masaccio/picow_day_clock/kicad/pico_dow_clock/pico_dow_clock.kicad_sch

## KiCad design kicad/pico_dow_clock/pico_dow_clock.kicad_sch (2026-08-09)

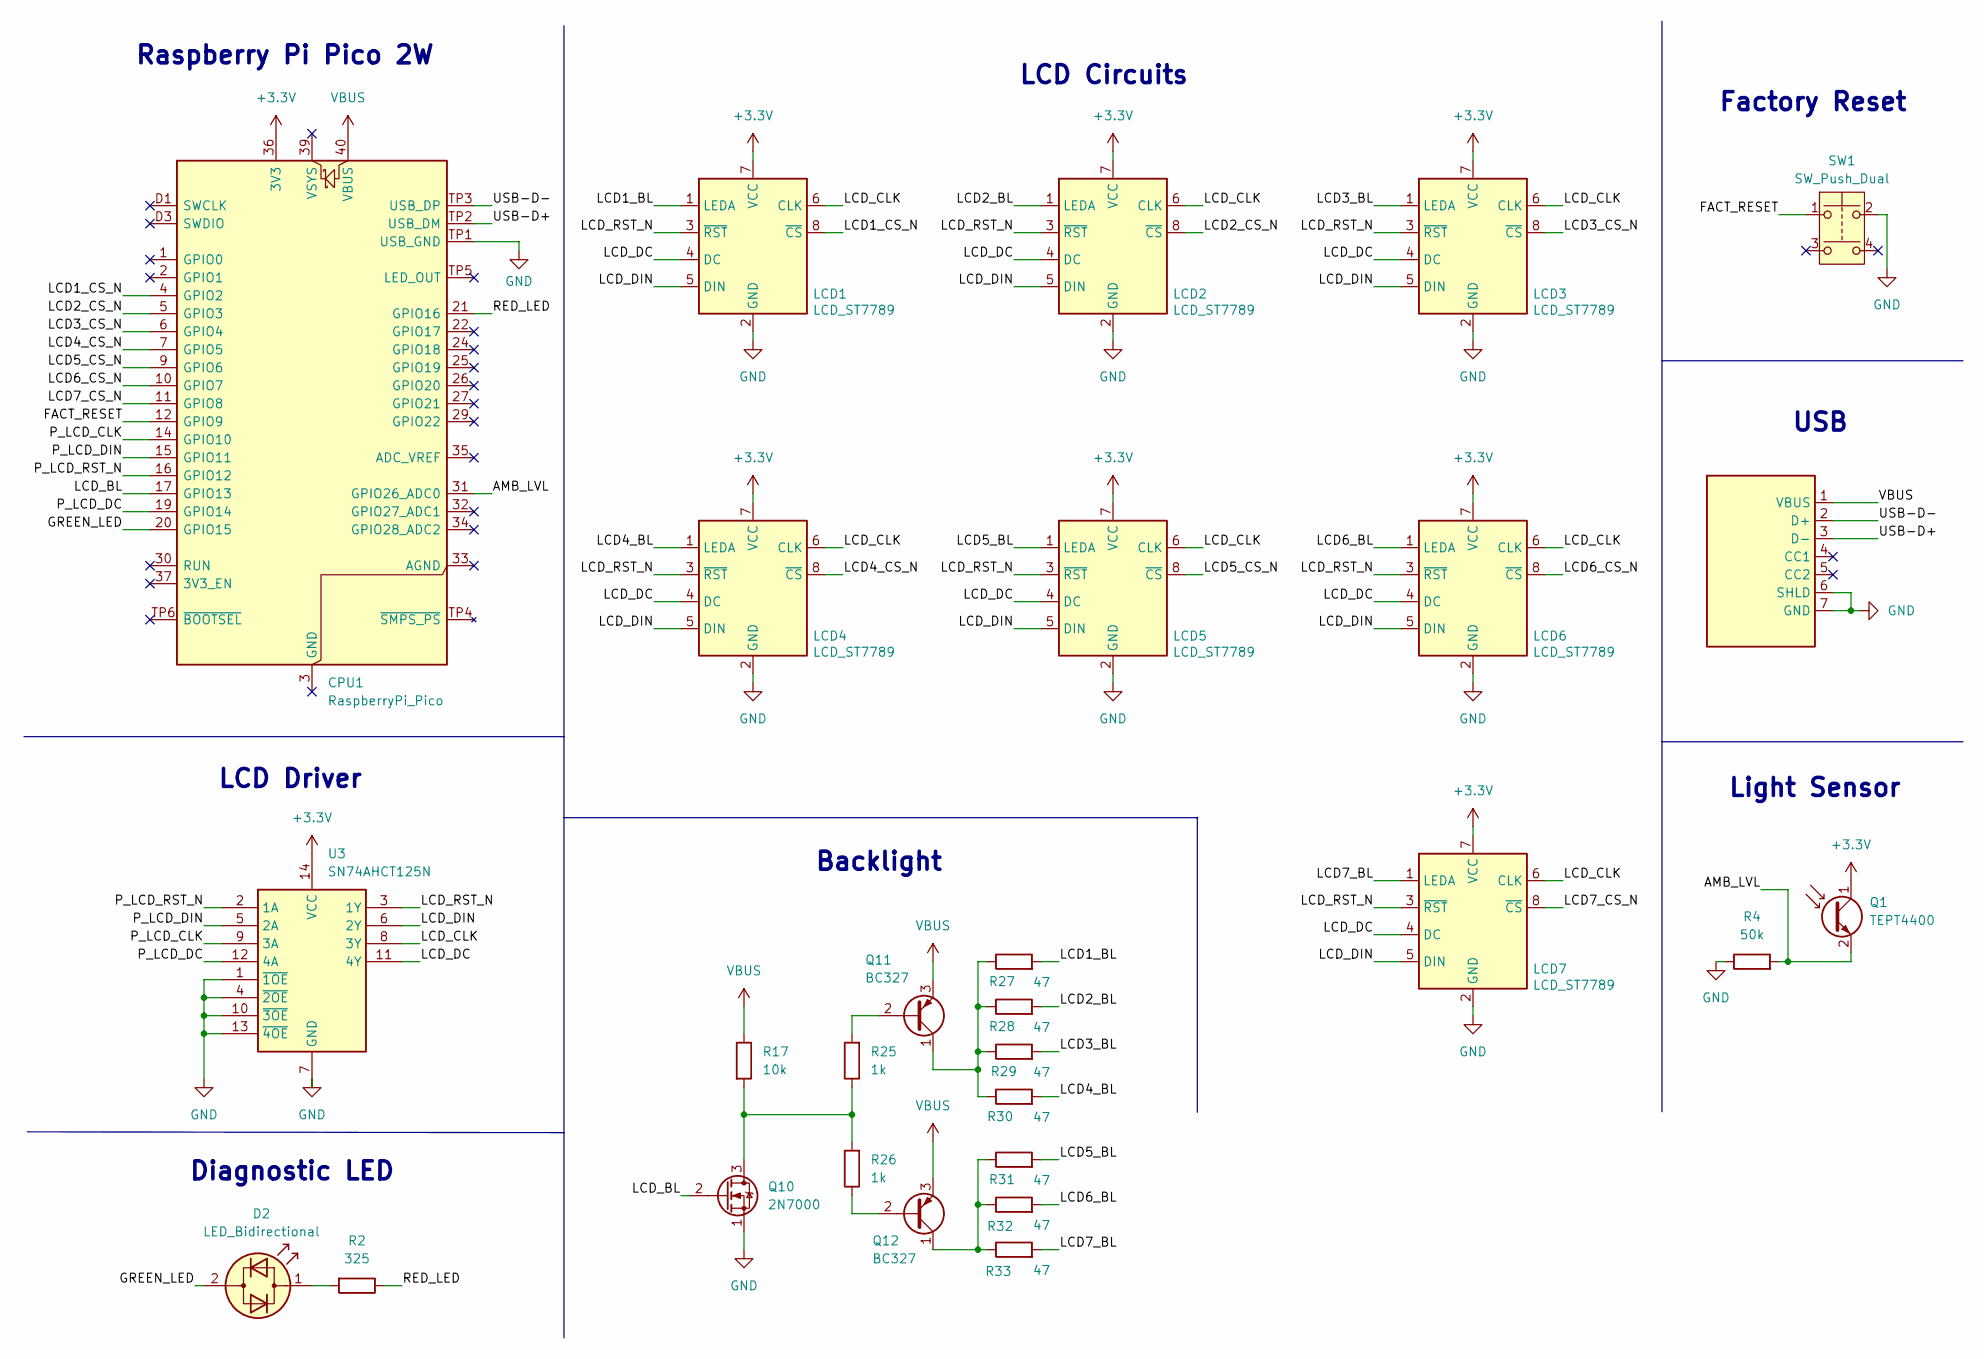
[picture p7: schematic pico_dow_clock.kicad_sch]

Parts:
CPU1: RaspberryPi_Pico; RaspberryPi_Pico_Original_SMD
D2: LED_Bidirectional
LCD1, LCD2, LCD3, LCD4, LCD5, LCD6, LCD7: LCD_ST7789
Q1: TEPT4400; LED_D3.0mm_Clear
Q10: 2N7000; TO-92_Inline
Q11, Q12: BC327; TO-92_Inline
R2: 325; R_Axial_DIN0207_L6.3mm_D2.5mm_P7.62mm_Horizontal
R4: 50k; R_Axial_DIN0207_L6.3mm_D2.5mm_P7.62mm_Horizontal
R17: 10k; R_Axial_DIN0207_L6.3mm_D2.5mm_P7.62mm_Horizontal
R25, R26: 1k; R_Axial_DIN0207_L6.3mm_D2.5mm_P7.62mm_Horizontal
R27, R28, R29, R30, R31, R32, R33: 47; R_Axial_DIN0207_L6.3mm_D2.5mm_P7.62mm_Horizontal
SW1: SW_Push_Dual
U3: SN74AHCT125N
USB1: Sparkfun_BOB_23055

Connections:
+3.3V: CPU1.36 (3V3), LCD1.7 (VCC), LCD2.7 (VCC), LCD3.7 (VCC), LCD4.7 (VCC), LCD5.7 (VCC), LCD6.7 (VCC), LCD7.7 (VCC), Q1.1 (C), U3.14 (VCC)
AMB_LVL: CPU1.31 (GPIO26_ADC0), Q1.2 (E), R4.2
FACT_RESET: CPU1.12 (GPIO9), SW1.1
GND: CPU1.TP1 (USB_GND), LCD1.2 (GND), LCD2.2 (GND), LCD3.2 (GND), LCD4.2 (GND), LCD5.2 (GND), LCD6.2 (GND), LCD7.2 (GND), Q10.1 (S), R4.1, SW1.2, U3.1 (~1OE), U3.4 (~2OE), U3.7 (GND), U3.10 (~3OE), U3.13 (~4OE), USB1.6 (SHLD), USB1.7 (GND)
GREEN_LED: CPU1.20 (GPIO15), D2.2 (AK)
LCD1_BL: LCD1.1 (LEDA), R27.2
LCD1_CS_N: CPU1.4 (GPIO2), LCD1.8 (~CS)
LCD2_BL: LCD2.1 (LEDA), R28.2
LCD2_CS_N: CPU1.5 (GPIO3), LCD2.8 (~CS)
LCD3_BL: LCD3.1 (LEDA), R29.2
LCD3_CS_N: CPU1.6 (GPIO4), LCD3.8 (~CS)
LCD4_BL: LCD4.1 (LEDA), R30.2
LCD4_CS_N: CPU1.7 (GPIO5), LCD4.8 (~CS)
LCD5_BL: LCD5.1 (LEDA), R31.2
LCD5_CS_N: CPU1.9 (GPIO6), LCD5.8 (~CS)
LCD6_BL: LCD6.1 (LEDA), R32.2
LCD6_CS_N: CPU1.10 (GPIO7), LCD6.8 (~CS)
LCD7_BL: LCD7.1 (LEDA), R33.2
LCD7_CS_N: CPU1.11 (GPIO8), LCD7.8 (~CS)
LCD_BL: CPU1.17 (GPIO13), Q10.2 (G)
LCD_CLK: LCD1.6 (CLK), LCD2.6 (CLK), LCD3.6 (CLK), LCD4.6 (CLK), LCD5.6 (CLK), LCD6.6 (CLK), LCD7.6 (CLK), U3.8 (3Y)
LCD_DC: LCD1.4 (DC), LCD2.4 (DC), LCD3.4 (DC), LCD4.4 (DC), LCD5.4 (DC), LCD6.4 (DC), LCD7.4 (DC), U3.11 (4Y)
LCD_DIN: LCD1.5 (DIN), LCD2.5 (DIN), LCD3.5 (DIN), LCD4.5 (DIN), LCD5.5 (DIN), LCD6.5 (DIN), LCD7.5 (DIN), U3.6 (2Y)
LCD_RST_N: LCD1.3 (~RST), LCD2.3 (~RST), LCD3.3 (~RST), LCD4.3 (~RST), LCD5.3 (~RST), LCD6.3 (~RST), LCD7.3 (~RST), U3.3 (1Y)
unnamed: CPU1.3 (GND), CPU1.8 (GND), CPU1.13 (GND), CPU1.18 (GND), CPU1.23 (GND), CPU1.28 (GND), CPU1.38 (GND), CPU1.D2 (GND)
unnamed: D2.1 (KA), R2.2
unnamed: Q10.3 (D), R17.2, R25.1, R26.2
unnamed: Q11.1 (C), R27.1, R28.1, R29.1, R30.1
unnamed: Q11.2 (B), R25.2
unnamed: Q12.1 (C), R31.1, R32.1, R33.1
unnamed: Q12.2 (B), R26.1
P_LCD_CLK: CPU1.14 (GPIO10), U3.9 (3A)
P_LCD_DC: CPU1.19 (GPIO14), U3.12 (4A)
P_LCD_DIN: CPU1.15 (GPIO11), U3.5 (2A)
P_LCD_RST_N: CPU1.16 (GPIO12), U3.2 (1A)
RED_LED: CPU1.21 (GPIO16), R2.1
USB-D+: CPU1.TP2 (USB_DM), USB1.3 (D-)
USB-D-: CPU1.TP3 (USB_DP), USB1.2 (D+)
VBUS: CPU1.40 (VBUS), Q11.3 (E), Q12.3 (E), R17.1, USB1.1 (VBUS)

Notes on the sheet:
Diagnostic LED
Factory Reset
USB
Raspberry Pi Pico 2W
LCD Circuits
LCD Driver
Light Sensor
Backlight
