masaccio/picow_day_clock/src/lcd.c

/*
 * SPDX-License-Identifier: MIT
 *
 * Much of this code is derived from the Waveshare 1.47inch LCD Module
 * driver (see https://www.waveshare.com/wiki/1.47inch_LCD_Module).
 *
 * (c) 2022 Waveshare team
 *
 * Additional code:
 *
 * (c) 2025 Jon Connell
 *
 */

#include <stdarg.h>
#include <stdio.h>
#include <stdlib.h>
#include <string.h>

// PICO SDK
#ifndef TEST_MODE
#include "hardware/pwm.h"
#include "hardware/spi.h"
#include "pico/stdlib.h"
#else
#include "mock.h"
#endif

// Local includes
#include "bitmap.h"
#include "clock.h"
#include "config.h"

// How the 2-bit colours map to 16-bit colour
static uint16_t color_table[] = LCD_COLOR_TABLE;

// PWM slice attached to the backlight
static uint slice_num;

// Current line number for diagnostics
static uint8_t line_number = 0;

// Shared line buffer to write a line at a time with spi_write_blocking()
uint8_t linebuf[LCD_WIDTH * 2];

static void st7789_init(lcd_state_t *state);

static void lcd_reset(lcd_state_t *state);

void lcd_write_image(lcd_state_t *state, const uint8_t *image, uint16_t x_start, uint16_t y_start, uint16_t image_width,
                     uint16_t image_height, color_t fg_color);

int lcd_write_char(lcd_state_t *state, uint16_t x_point, uint16_t y_point, const char ascii_char, font_t *font,
                   color_t fg_color, color_t bg_color);

lcd_state_t *lcd_init(lcd_state_t *state, uint16_t lcd_num, bool reset)

{
    state->RST_N_gpio = LCD_GPIO_RST_N;
    state->DC_gpio = LCD_GPIO_DC;
    state->BL_gpio = LCD_GPIO_BL;
    state->CS_N_gpio = LCD_GPIO_CS_N_BASE + lcd_num;
    state->CLK_gpio = LCD_GPIO_CLK;
    state->MOSI_gpio = LCD_GPIO_MOSI;
    state->smoothed_adc = 0;

    lcd_init_peripherals(state, reset);
    lcd_set_backlight(state, 90);
    if (reset) {
        // All displays share the same reset line
        lcd_reset(state);
    }

    st7789_init(state);
    lcd_clear_screen(state, BG_COLOR);

    return state;
}

void lcd_print_line(lcd_state_t *state, color_t color, lcd_status_message_t msg)
{
    uint16_t y_start = (line_number + 3) * text_font.height;
    uint16_t x_point = 0;
    uint16_t y_point = y_start;
    int width = 0;
    const char *msg_str;
    switch (msg) {
        case LCD_MSG_INIT_OK:
            msg_str = LCD_MSG_STR_INIT_OK;
            break;
        case LCD_MSG_FLASH_ERROR:
            msg_str = LCD_MSG_STR_FLASH_ERROR;
            break;
        case LCD_MSG_WIFI_ERROR:
            msg_str = LCD_MSG_STR_WIFI_ERROR;
            break;
        case LCD_MSG_WIFI_OK:
            msg_str = LCD_MSG_STR_WIFI_OK;
            break;
    }
    while (*msg_str != '\0') {
        // Wrap end of line
        if ((x_point + width) > LCD_WIDTH) {
            x_point = 0;
            y_point += text_font.height;
        }

        // Wrap end of screen
        if ((y_point + text_font.height) > LCD_HEIGHT) {
            x_point = 0;
            y_point = 0;
        }
        width = lcd_write_char(state, x_point, y_point, *msg_str, &text_font, color, BG_COLOR);
        x_point += width;
        msg_str++;
    }
    line_number++;
}

void lcd_print_clock_digit(lcd_state_t *state, color_t color, const char ascii_char)
{
    if (ascii_char < ' ' || ascii_char > '~') {
        return;
    }
    const font_glyph_t entry = clock_digit_font.table[ascii_char - ' '];
    uint16_t x_point = (LCD_WIDTH - entry.width) / 2;
    (void)lcd_write_char(state, x_point, 0, ascii_char, &clock_digit_font, color, BLACK);
}

#define ICON_CASE(STATUS, ICON, OFFSET, COLOR)                                                                         \
    case STATUS:                                                                                                       \
        lcd_write_image(state, ICON, OFFSET, 0, ICON_SIZE, ICON_SIZE, COLOR);                                          \
        break;

void lcd_update_icons(lcd_state_t *state, watchdog_error_t watchdog_error, ntp_error_t ntp_error,
                      wifi_error_t wifi_error)
{
    switch (watchdog_error) {
        ICON_CASE(WATCHDOG_RESET, watchdog_icon, WATCHDOG_ICON_X_OFFSET, RED)
        ICON_CASE(WATCHDOG_NTP, watchdog_ntp_icon, WATCHDOG_ICON_X_OFFSET, RED)
        ICON_CASE(WATCHDOG_WIFI, watchdog_wifi_icon, WATCHDOG_ICON_X_OFFSET, RED)
        case WATCHDOG_OK:
            break;
    }
    switch (ntp_error) {
        ICON_CASE(NTP_OK, ntp_icon, NTP_ICON_X_OFFSET, GREEN)
        ICON_CASE(NTP_INIT_ERROR, ntp_init_icon, NTP_ICON_X_OFFSET, RED)
        ICON_CASE(NTP_DNS_ERROR, ntp_dns_icon, NTP_ICON_X_OFFSET, RED)
        ICON_CASE(NTP_MEMORY_ERROR, ntp_memory_icon, NTP_ICON_X_OFFSET, RED)
        ICON_CASE(NTP_PROTOCOL_ERROR, ntp_error_icon, NTP_ICON_X_OFFSET, RED)
        ICON_CASE(NTP_TIMEOUT_ERROR, ntp_timeout_icon, NTP_ICON_X_OFFSET, RED)
    }
    switch (wifi_error) {
        ICON_CASE(WIFI_OK, wifi_icon, WIFI_ICON_X_OFFSET, GREEN)
        ICON_CASE(WIFI_INIT_ERROR, wifi_init_icon, WIFI_ICON_X_OFFSET, RED)
        ICON_CASE(WIFI_TIMEOUT_ERROR, wifi_timeout_icon, WIFI_ICON_X_OFFSET, RED)
        ICON_CASE(WIFI_AUTH_ERROR, wifi_password_icon, WIFI_ICON_X_OFFSET, RED)
        ICON_CASE(WIFI_CONNECT_ERROR, wifi_connect_icon, WIFI_ICON_X_OFFSET, RED)
        ICON_CASE(WIFI_UNKNOWN_ERROR, wifi_error_icon, WIFI_ICON_X_OFFSET, RED)
    }
}

// Initialise the Pico peripherals we will use (SPI, GPIO, PWM)
void lcd_init_peripherals(lcd_state_t *state, int reset)
{
    spi_init(spi1, 10000 * 1000);
    gpio_set_function(state->CLK_gpio, GPIO_FUNC_SPI);
    gpio_set_function(state->MOSI_gpio, GPIO_FUNC_SPI);

    if (reset) {
        gpio_init(state->RST_N_gpio);
        gpio_set_dir(state->RST_N_gpio, GPIO_OUT);
    }
    gpio_init(state->DC_gpio);
    gpio_set_dir(state->DC_gpio, GPIO_OUT);
    gpio_init(state->CS_N_gpio);
    gpio_set_dir(state->CS_N_gpio, GPIO_OUT);
    gpio_init(state->BL_gpio);
    gpio_set_dir(state->BL_gpio, GPIO_OUT);

    gpio_put(state->CS_N_gpio, 1);
    gpio_put(state->DC_gpio, 0);
    gpio_put(state->BL_gpio, 1);

    gpio_set_function(state->BL_gpio, GPIO_FUNC_PWM);
    slice_num = (uint)pwm_gpio_to_slice_num(state->BL_gpio);
    pwm_set_wrap(slice_num, 100);
    pwm_set_chan_level(slice_num, PWM_CHAN_B, 1);
    pwm_set_clkdiv(slice_num, 50);
    pwm_set_enabled(slice_num, 1);
}

// Use the PWM to set the backlight level for all displays
void lcd_set_backlight(lcd_state_t *state, uint8_t level)
{
    (void)state;
    if (level > 100) {
        level = 100;
    }
    pwm_set_chan_level(slice_num, PWM_CHAN_B, level);
}

// Cycle reset for all displays
static void lcd_reset(lcd_state_t *state)
{
    gpio_put(state->RST_N_gpio, 1);
    sleep_ms(100);
    gpio_put(state->RST_N_gpio, 0);
    sleep_ms(100);
    gpio_put(state->RST_N_gpio, 1);
    sleep_ms(100);
}

// Select an LCD and send a command byte
static void st7789_command(lcd_state_t *state, uint8_t reg)
{
    gpio_put(state->DC_gpio, 0);
    gpio_put(state->CS_N_gpio, 0);
    spi_write_blocking(spi1, &reg, 1);
    gpio_put(state->CS_N_gpio, 1);
}

// Select an LCD and send a data byte
static void st7789_data_byte(lcd_state_t *state, uint8_t data)
{
    gpio_put(state->DC_gpio, 1);
    gpio_put(state->CS_N_gpio, 0);
    spi_write_blocking(spi1, &data, 1);
    gpio_put(state->CS_N_gpio, 1);
}

static void st7789_init(lcd_state_t *state)
{

    st7789_command(state, 0x11); // SLPOUT (Sleep Out)

    sleep_ms(120);

    st7789_command(state, 0x36); // MADCTL (Memory Data Access Control)
    st7789_data_byte(state, 0x00);

    st7789_command(state, 0x3A); // COLMOD (Interface Pixel Format)
    st7789_data_byte(state, 0x05);

    st7789_command(state, 0xB2); // PORCTRL (Porch Setting)
    st7789_data_byte(state, 0x0C);
    st7789_data_byte(state, 0x0C);
    st7789_data_byte(state, 0x00);
    st7789_data_byte(state, 0x33);
    st7789_data_byte(state, 0x33);

    st7789_command(state, 0xB7); // GCTRL (Gate Control)
    st7789_data_byte(state, 0x35);

    st7789_command(state, 0xBB); // VCOMS (VCOM Setting)
    st7789_data_byte(state, 0x35);

    st7789_command(state, 0xC0); // LCMCTRL (LCM Control)
    st7789_data_byte(state, 0x2C);

    st7789_command(state, 0xC2); // VDVVRHEN (VDV and VRH Command Enable)
    st7789_data_byte(state, 0x01);

    st7789_command(state, 0xC3); // VRHS (VRH Set)
    st7789_data_byte(state, 0x13);

    st7789_command(state, 0xC4); // VDVS (VDV Set)
    st7789_data_byte(state, 0x20);

    st7789_command(state, 0xC6); // FRCTRL2 (Frame Rate Control in Normal Mode)
    st7789_data_byte(state, 0x0F);

    st7789_command(state, 0xD0); // PWCTRL1 (Power Control 1)
    st7789_data_byte(state, 0xA4);
    st7789_data_byte(state, 0xA1);

    st7789_command(state, 0xD6); // !!! Non-standard command
    st7789_data_byte(state, 0xA1);

    st7789_command(state, 0xE0); // PVGAMCTRL (Positive Voltage Gamma Control)
    st7789_data_byte(state, 0xF0);
    st7789_data_byte(state, 0x00);
    st7789_data_byte(state, 0x04);
    st7789_data_byte(state, 0x04);
    st7789_data_byte(state, 0x04);
    st7789_data_byte(state, 0x05);
    st7789_data_byte(state, 0x33);
    st7789_data_byte(state, 0x3E);
    st7789_data_byte(state, 0x38);
    st7789_data_byte(state, 0x12);
    st7789_data_byte(state, 0x12);
    st7789_data_byte(state, 0x28);
    st7789_data_byte(state, 0x30);

    st7789_command(state, 0xE1); // NVGAMCTRL (Negative Voltage Gamma Control)
    st7789_data_byte(state, 0xF0);
    st7789_data_byte(state, 0x07);
    st7789_data_byte(state, 0x0A);
    st7789_data_byte(state, 0x0D);
    st7789_data_byte(state, 0x0B);
    st7789_data_byte(state, 0x07);
    st7789_data_byte(state, 0x28);
    st7789_data_byte(state, 0x33);
    st7789_data_byte(state, 0x3E);
    st7789_data_byte(state, 0x36);
    st7789_data_byte(state, 0x14);
    st7789_data_byte(state, 0x14);
    st7789_data_byte(state, 0x32);

    st7789_command(state, 0x21); // INVON (Display Inversion On)

    st7789_command(state, 0x11); // SLPOUT (Sleep Out)

    sleep_ms(120);

    st7789_command(state, 0x29); // DISPON (Display On)
}

static void st7789_set_command_windows(lcd_state_t *state, uint16_t x_start, uint16_t y_start, uint16_t width,
                                       uint16_t height)
{

    // X-coordinates are based on portrait mode
    st7789_command(state, 0x2A); // CASET (Column address set)
    st7789_data_byte(state, (x_start + LCD_ROW_START) >> 8);
    st7789_data_byte(state, (x_start + LCD_ROW_START) & 0xff);
    st7789_data_byte(state, (x_start + width + LCD_ROW_START - 1) >> 8);
    st7789_data_byte(state, (x_start + width + LCD_ROW_START - 1) & 0xff);

    // Set the Y coordinates
    st7789_command(state, 0x2B); // RASET (Row address set)
    st7789_data_byte(state, (y_start + LCD_COL_START) >> 8);
    st7789_data_byte(state, (y_start + LCD_COL_START) & 0xff);
    st7789_data_byte(state, (y_start + height + LCD_COL_START - 1) >> 8);
    st7789_data_byte(state, (y_start + height + LCD_COL_START - 1) & 0xff);

    st7789_command(state, 0x2C); // RAMWR (Memory Write)
}

void lcd_draw_rectangle(lcd_state_t *state, uint16_t x_start, uint16_t y_start, uint16_t width, uint16_t height,
                        uint16_t fg_color)
{
    st7789_set_command_windows(state, x_start, y_start, width, height);
    gpio_put(state->DC_gpio, 1);
    gpio_put(state->CS_N_gpio, 0);

    uint8_t fg_hi = color_table[fg_color % 4] >> 8;
    uint8_t fg_lo = color_table[fg_color % 4] & 0xFF;
    for (uint16_t x = 0; x < width; x++) {
        linebuf[x * 2] = fg_hi;
        linebuf[x * 2 + 1] = fg_lo;
    }

    for (uint16_t j = 0; j < height; j++) {
        spi_write_blocking(spi1, (uint8_t *)linebuf, width * 2);
    }
    gpio_put(state->CS_N_gpio, 1);
}

void lcd_clear_screen(lcd_state_t *state, uint16_t color)
{
    line_number = 0;
    lcd_draw_rectangle(state, 0, 0, LCD_WIDTH, LCD_HEIGHT, color);
}

int lcd_write_char(lcd_state_t *state, uint16_t x_point, uint16_t y_point, const char ascii_char, font_t *font,
                   color_t fg_color, color_t bg_color)
{
    if (ascii_char < ' ' || ascii_char > '~') {
        return 0;
    }
    const font_glyph_t *entry = &font->table[ascii_char - ' '];
    const uint8_t *ptr = entry->table;
    uint16_t font_width = entry->width;

    st7789_set_command_windows(state, x_point, y_point, font_width, font->height);
    gpio_put(state->DC_gpio, 1);
    gpio_put(state->CS_N_gpio, 0);

    uint8_t fg_hi = color_table[fg_color % 4] >> 8;
    uint8_t fg_lo = color_table[fg_color % 4] & 0xFF;
    uint8_t bg_hi = color_table[bg_color % 4] >> 8;
    uint8_t bg_lo = color_table[bg_color % 4] & 0xFF;

    for (uint16_t glyph_row = 0; glyph_row < font->height; glyph_row++) {
        for (uint16_t glyph_column = 0; glyph_column < font_width; glyph_column++) {
            uint8_t glyph_pixels = *(ptr + (glyph_column / 8));
            if (glyph_pixels & (0x80 >> (glyph_column % 8))) {
                linebuf[glyph_column * 2] = fg_hi;
                linebuf[glyph_column * 2 + 1] = fg_lo;
            } else {
                linebuf[glyph_column * 2] = bg_hi;
                linebuf[glyph_column * 2 + 1] = bg_lo;
            }
        }
        spi_write_blocking(spi1, (uint8_t *)linebuf, font_width * 2);
        ptr += font->byte_width;
    }

    gpio_put(state->CS_N_gpio, 1);

    return font_width;
}

void lcd_write_image(lcd_state_t *state, const uint8_t *image, uint16_t x_start, uint16_t y_start, uint16_t image_width,
                     uint16_t image_height, color_t fg_color)
{
    st7789_set_command_windows(state, x_start, y_start, image_width, image_height);
    gpio_put(state->DC_gpio, 1);
    gpio_put(state->CS_N_gpio, 0);

    int bytes_per_row = (image_width + 7) / 8;
    for (int yy = 0; yy < image_height; yy++) {
        for (int byte_idx = 0; byte_idx < bytes_per_row; byte_idx++) {
            uint8_t byte = *image++;
            for (int bit = 0; bit < 8; bit++) {
                int x = x_start + (byte_idx * 8) + bit;
                if (x < x_start + image_width) {
                    // Most significant bit is left-most pixel
                    linebuf[(x - x_start) * 2] = color_table[(byte & (1 << (7 - bit))) ? fg_color : 0] >> 8;
                    linebuf[(x - x_start) * 2 + 1] = color_table[(byte & (1 << (7 - bit))) ? fg_color : 0] & 0xFF;
                }
            }
        }
        spi_write_blocking(spi1, (uint8_t *)linebuf, image_width * 2);
    }
    gpio_put(state->CS_N_gpio, 1);
}
