masaccio/picow_day_clock/src/bitmap.h

#pragma once

#include <stdint.h>

typedef struct
{
    const uint8_t *table;
    const uint8_t width;
} font_glyph_t;

typedef struct
{
    const font_glyph_t *table;
    uint16_t byte_width;
    uint16_t height;
} font_t;

extern font_t text_font;
extern font_t clock_digit_font;

#define ICON_SIZE 36
#define BYTES_PER_ROW (ICON_SIZE + 7) / 8
#define ICON_BYTES (BYTES_PER_ROW * ICON_SIZE)

// Allow 5 pixels for the rounded edge
#define WATCHDOG_ICON_X_OFFSET (uint16_t)(LCD_WIDTH - 5 + ICON_SIZE * -3)
#define NTP_ICON_X_OFFSET (uint16_t)(LCD_WIDTH - 5 + ICON_SIZE * -2)
#define WIFI_ICON_X_OFFSET (uint16_t)(LCD_WIDTH - 5 + ICON_SIZE * -1)

extern const uint8_t memory_icon[ICON_BYTES];
extern const uint8_t watchdog_icon[ICON_BYTES];
extern const uint8_t watchdog_wifi_icon[ICON_BYTES];
extern const uint8_t watchdog_ntp_icon[ICON_BYTES];
extern const uint8_t wifi_icon[ICON_BYTES];
extern const uint8_t ntp_icon[ICON_BYTES];
extern const uint8_t wifi_init_icon[ICON_BYTES];
extern const uint8_t wifi_timeout_icon[ICON_BYTES];
extern const uint8_t wifi_password_icon[ICON_BYTES];
extern const uint8_t wifi_connect_icon[ICON_BYTES];
extern const uint8_t wifi_error_icon[ICON_BYTES];
extern const uint8_t ntp_init_icon[ICON_BYTES];
extern const uint8_t ntp_dns_icon[ICON_BYTES];
extern const uint8_t ntp_timeout_icon[ICON_BYTES];
extern const uint8_t ntp_memory_icon[ICON_BYTES];
extern const uint8_t ntp_error_icon[ICON_BYTES];
