masaccio/picow_day_clock/tests/tests.c

#include <stdbool.h>
#include <stdio.h>
#include <stdlib.h>
#include <string.h>
#include <time.h>

#include "clock.h"
#include "config.h"
#include "test.h"

// These system calls have been redefined in mock.h so undef them here
// so that we can call into the system libraries as needed.
#undef printf
#undef calloc
#undef free

typedef int (*test_func_t)(void);
static unsigned int test_verbose = 0;

mock_context_t mock_ctx = {0};
#define RESET_MOCK_CONFIG()                                                                                            \
    do {                                                                                                               \
        memset((void *)&mock_ctx.inject, 0, sizeof(mock_ctx.inject));                                                  \
        memset((void *)&mock_ctx.spy, 0, sizeof(mock_ctx.spy));                                                        \
        mock_ctx.sim.dns_pending = false;                                                                              \
        mock_ctx.sim.udp_pending = false;                                                                              \
        mock_ctx.sim.clock_timer_active = false;                                                                       \
        mock_ctx.sim.backlight_timer_active = false;                                                                   \
        icon_queue_t_init(&mock_ctx.spy.icon_history);                                                                 \
        lcd_message_queue_t_init(&mock_ctx.spy.lcd_msg_history);                                                       \
    } while (0)

#define TEST_AP_SSID "HomeNet"
#define TEST_AP_PASSWORD "s3cr3t"
#define TEST_NTP_SERVER "time.apple.com"
#define TEST_TZ_OFFSET 0
#define TEST_DST_RULE DST_RULE_NONE
#define TEST_TIMEOUT 10 * 1000
#define TEST_NTP_PORT 8123

#define FILENAME (strrchr(__FILE__, '/') ? strrchr(__FILE__, '/') + 1 : __FILE__)
#define ASSERT_WITH_MESSAGE(a, b, msg)                                                                                 \
    do {                                                                                                               \
        if ((a) != (b)) {                                                                                              \
            printf("ASSERT FAILED: %s:%d: %s\n", FILENAME, __LINE__, (msg));                                           \
            return 1;                                                                                                  \
        } else if (mock_ctx.config.test_verbose) {                                                                     \
            printf("ASSERT OK: %s:%d: %s\n", FILENAME, __LINE__, (msg));                                               \
        }                                                                                                              \
    } while (0)

#define CHECK_ICONS_OK()                                                                                               \
    do {                                                                                                               \
        ASSERT_WITH_MESSAGE(mock_ctx.spy.watchdog_icon, WATCHDOG_OK, "Watchdog OK");                                   \
        ASSERT_WITH_MESSAGE(mock_ctx.spy.ntp_icon, NTP_OK, "NTP  OK");                                                 \
        ASSERT_WITH_MESSAGE(mock_ctx.spy.wifi_icon, WIFI_OK, "Wi-Fi OK");                                              \
    } while (0)
#define CHECK_WATCHDOG_RESET_OK()                                                                                      \
    do {                                                                                                               \
        ASSERT_WITH_MESSAGE(mock_ctx.spy.watchdog_icon, WATCHDOG_RESET, "Watchdog reset");                             \
        ASSERT_WITH_MESSAGE(mock_ctx.spy.ntp_icon, NTP_OK, "NTP  OK");                                                 \
        ASSERT_WITH_MESSAGE(mock_ctx.spy.wifi_icon, WIFI_OK, "Wi-Fi OK");                                              \
    } while (0)
#define CHECK_ICONS_FAIL(N, WATCHDOG, NTP, WIFI)                                                                       \
    do {                                                                                                               \
        ASSERT_WITH_MESSAGE(mock_ctx.spy.watchdog_icon, WATCHDOG, "Watchdog fail status");                             \
        ASSERT_WITH_MESSAGE(mock_ctx.spy.ntp_icon, NTP, "NTP  fail status");                                           \
        ASSERT_WITH_MESSAGE(mock_ctx.spy.wifi_icon, WIFI, "Wi-Fi fail status");                                        \
    } while (0)
#define EXPECT_FATAL_NTP_ERROR(ERROR)                                                                                  \
    do {                                                                                                               \
        CHECK_ICONS_FAIL(0, WATCHDOG_NTP, (ERROR), WIFI_OK);                                                           \
        ASSERT_WITH_MESSAGE(mock_ctx.spy.fatal_reset_caught, 1, "Fatal reset caught");                                 \
        ASSERT_WITH_MESSAGE(mock_ctx.spy.fatal_wifi_error, WIFI_OK, "Wi-Fi OK");                                       \
        ASSERT_WITH_MESSAGE(mock_ctx.spy.fatal_ntp_error, ERROR, "NTP error type");                                    \
    } while (0)
#define EXPECT_FATAL_WIFI_ERROR(ERROR)                                                                                 \
    do {                                                                                                               \
        CHECK_ICONS_FAIL(0, WATCHDOG_WIFI, NTP_OK, (ERROR));                                                           \
        ASSERT_WITH_MESSAGE(mock_ctx.spy.fatal_reset_caught, 1, "Fatal reset caught");                                 \
        ASSERT_WITH_MESSAGE(mock_ctx.spy.fatal_wifi_error, ERROR, "Wi-Fi error type");                                 \
    } while (0)

#define EXPECT_OK 0
#define EXPECT_FAIL 1
#define EXECUTE_TEST_WRAPPER(test_func, msg, status)                                                                   \
    do {                                                                                                               \
        if (test_func != status) {                                                                                     \
            test_printf("CHECK: TEST FAIL: " msg ", %s:%d\n", FILENAME, __LINE__);                                     \
            return 1;                                                                                                  \
        } else {                                                                                                       \
            test_printf("CHECK: TEST OK: " msg "\n");                                                                  \
        }                                                                                                              \
    } while (0)
#define EXECUTE_TEST(msg, status) EXECUTE_TEST_WRAPPER(test_main(), msg, status)

#define EXPECT_LCD_DIGITS(str)                                                                                         \
    do {                                                                                                               \
        if (strncmp(clock_state->current_lcd_digits, str, 7) != 0) {                                                   \
            printf("ASSERT FAILED: LCD state is %s not %s\n", clock_state->current_lcd_digits, str);                   \
            return 1;                                                                                                  \
        }                                                                                                              \
    } while (0)

static bool mock_store_config_success(struct flash_config_t *config, bool invalidate);
static bool mock_store_config_fail_then_success(struct flash_config_t *config, bool invalidate);

static void set_localtime(clock_state_t *clock_state, int year, int mon, int mday, int hour, int min, int sec)
{

    struct tm tm_val = {0};
    tm_val.tm_year = year - 1900;
    tm_val.tm_mon = mon;
    tm_val.tm_mday = mday;
    tm_val.tm_hour = hour;
    tm_val.tm_min = min;
    tm_val.tm_sec = sec;
    tm_val.tm_isdst = 0;
    time_t t = tm_to_epoch(&tm_val);

    clock_state->ntp_last_sync = t;
    clock_state->ntp_interval = NTP_SYNC_INTERVAL_SEC;
    mock_ctx.spy.system_time_ms = t * 1000;
    mock_ctx.spy.boot_time_ms = t * 1000;
    mock_ctx.spy.ntp_seconds = (mock_ctx.spy.system_time_ms / 1000) + NTP_DELTA;
    mock_ctx.sim.clock_timer_next_fire = mock_ctx.spy.boot_time_ms + 1000;
}

static clock_state_t *create_test_clock_state(repeating_timer_t *timer, flash_config_t *flash_config)
{
    static clock_state_t clock_state;
    memset(&clock_state, 0, sizeof(clock_state_t));
    for (uint16_t ii = 0; ii < NUM_LCDS; ii++) {
        lcd_init(&clock_state.lcd_states[ii], ii, /* reset */ ii == 0);
    }
    ntp_init(&clock_state.ntp_state, (void *)&clock_state, ntp_timer_callback);
    clock_state.ntp_last_sync = mock_time(NULL);
    clock_state.ntp_time = clock_state.ntp_last_sync;
    clock_state.ntp_state.ntp_port = TEST_NTP_PORT;
    clock_state.first_clock_tick = false;
    timer->user_data = &clock_state;

    memcpy(&clock_state.flash_config, flash_config, sizeof(flash_config_t));
    memcpy(mock_flash_config, flash_config, sizeof(flash_config_t));

    add_repeating_timer_ms(1000, clock_timer_callback, &clock_state, timer);

    return &clock_state;
}

static flash_config_t *create_flash_config(void)
{
    static flash_config_t flash_config = {.magic_marker = CONFIG_MAGIC,
                                          .wifi_ssid = TEST_AP_SSID,
                                          .wifi_password = TEST_AP_PASSWORD,
                                          .tz_offset_mins = TEST_TZ_OFFSET,
                                          .dst_rule = (dst_rule_t)TEST_DST_RULE,
                                          .ntp_timeout = TEST_TIMEOUT,
                                          .ntp_port = TEST_NTP_PORT};
    return &flash_config;
}

static int run_test(test_func_t func, const char *test_name)
{
    // Always init the shared test context.
    memset(&mock_ctx, 0, sizeof(mock_ctx));
    mock_ctx.config.test_verbose = test_verbose;
    mock_ctx.config.udp_port = TEST_NTP_PORT;

    test_printf("Starting test '%s'\n", test_name);

    // Run test
    int status = func();

    printf("TEST %s: %s\n", test_name, (status == 1) ? "FAIL" : "OK");
    return status;
}

static int test_lcd(void)
{
    RESET_MOCK_CONFIG();
    mock_ctx.inject.adc_level = (AMBIENT_LIGHT_BRIGHT / 2);
    mock_ctx.inject.exit_after_ms = 5000;
    EXECUTE_TEST("LCD brightness", EXPECT_OK);
    ASSERT_WITH_MESSAGE(mock_ctx.spy.lcd_brightness, 63, "LCD brightness");

    RESET_MOCK_CONFIG();
    mock_ctx.inject.adc_level = AMBIENT_LIGHT_DARK - 1;
    mock_ctx.inject.exit_after_ms = 5000;
    EXECUTE_TEST("LCD brightness", EXPECT_OK);
    ASSERT_WITH_MESSAGE(mock_ctx.spy.lcd_brightness, 5, "LCD minimum brightness");

    RESET_MOCK_CONFIG();
    mock_ctx.inject.adc_level = 0xfff;
    mock_ctx.inject.exit_after_ms = 5000;
    EXECUTE_TEST("LCD brightness", EXPECT_OK);
    ASSERT_WITH_MESSAGE(mock_ctx.spy.lcd_brightness, 100, "LCD maximum brightness");
    return 0;
}

static int test_dns_lookups(void)
{
    RESET_MOCK_CONFIG();
    mock_ctx.inject.dns_bad_arg = 1;
    EXECUTE_TEST("DNS bad arg", EXPECT_FAIL);
    EXPECT_FATAL_NTP_ERROR(NTP_DNS_ERROR);

    RESET_MOCK_CONFIG();
    mock_ctx.inject.dns_lookup_fail = 1;
    EXECUTE_TEST("DNS lookup failure", EXPECT_FAIL);
    EXPECT_FATAL_NTP_ERROR(NTP_DNS_ERROR);

    RESET_MOCK_CONFIG();
    mock_ctx.inject.dns_latency_ms = TEST_TIMEOUT + 1000;
    EXECUTE_TEST("DNS timeout", EXPECT_FAIL);
    EXPECT_FATAL_NTP_ERROR(NTP_TIMEOUT_ERROR);

    RESET_MOCK_CONFIG();
    mock_ctx.inject.dns_latency_ms = TEST_TIMEOUT - 1000;
    mock_ctx.inject.exit_on_ntp_success = 1;
    EXECUTE_TEST("DNS delay", EXPECT_OK);
    CHECK_ICONS_OK();

    return 0;
}

static int test_connect_to_wifi_direct(void)
{
    RESET_MOCK_CONFIG();
    bool wifi_initialized = false;
    wifi_error_t err = connect_to_wifi("ssid", "pass", &wifi_initialized);
    ASSERT_WITH_MESSAGE(err, WIFI_OK, "connect_to_wifi should succeed");
    ASSERT_WITH_MESSAGE(wifi_initialized, true, "connect_to_wifi should mark initialized");

    RESET_MOCK_CONFIG();
    mock_ctx.inject.cyw43_arch_init_fail = 1;
    wifi_initialized = false;
    err = connect_to_wifi("ssid", "pass", &wifi_initialized);
    ASSERT_WITH_MESSAGE(err, WIFI_INIT_ERROR, "connect_to_wifi should fail on init error");
    ASSERT_WITH_MESSAGE(wifi_initialized, false, "connect_to_wifi should not mark initialized on init failure");

    RESET_MOCK_CONFIG();
    mock_ctx.inject.cyw43_auth_error_count = WIFI_BAD_AUTH_RETRY_COUNT;
    wifi_initialized = false;
    err = connect_to_wifi("ssid", "pass", &wifi_initialized);
    ASSERT_WITH_MESSAGE(err, WIFI_AUTH_ERROR, "connect_to_wifi should fail after repeated auth errors");

    RESET_MOCK_CONFIG();
    mock_ctx.inject.cyw43_auth_timeout_count = 4;
    wifi_initialized = false;
    err = connect_to_wifi("ssid", "pass", &wifi_initialized);
    ASSERT_WITH_MESSAGE(err, WIFI_TIMEOUT_ERROR, "connect_to_wifi should fail after repeated timeouts");

    RESET_MOCK_CONFIG();
    mock_ctx.inject.cyw43_arch_wifi_connect_status = PICO_ERROR_CONNECT_FAILED;
    wifi_initialized = false;
    err = connect_to_wifi("ssid", "pass", &wifi_initialized);
    ASSERT_WITH_MESSAGE(err, WIFI_CONNECT_ERROR, "connect_to_wifi should fail on connect failure");

    RESET_MOCK_CONFIG();
    mock_ctx.inject.cyw43_arch_wifi_connect_status = -99;
    wifi_initialized = false;
    err = connect_to_wifi("ssid", "pass", &wifi_initialized);
    ASSERT_WITH_MESSAGE(err, WIFI_UNKNOWN_ERROR, "connect_to_wifi should fail on unknown status");

    return 0;
}

static int test_start_wifi_access_point_direct(void)
{
    RESET_MOCK_CONFIG();
    mock_ctx.inject.tcp_open_fail = 1;
    bool wifi_initialized = false;
    wifi_error_t err = start_wifi_access_point(NULL, mock_store_config_success, &wifi_initialized);
    ASSERT_WITH_MESSAGE(err, WIFI_INIT_ERROR, "AP startup should fail when TCP setup fails");

    return 0;
}

static int test_wifi_errors(void)
{
    RESET_MOCK_CONFIG();
    mock_ctx.inject.cyw43_arch_init_fail = 1;
    EXECUTE_TEST("Wi-Fi init failure", EXPECT_FAIL);
    EXPECT_FATAL_WIFI_ERROR(WIFI_INIT_ERROR);

    RESET_MOCK_CONFIG();
    mock_ctx.inject.cyw43_arch_wifi_connect_status = PICO_ERROR_CONNECT_FAILED;
    EXECUTE_TEST("Wi-Fi connect failure", EXPECT_FAIL);
    EXPECT_FATAL_WIFI_ERROR(WIFI_CONNECT_ERROR);

    RESET_MOCK_CONFIG();
    mock_ctx.inject.cyw43_arch_wifi_connect_status = -99;
    EXECUTE_TEST("Wi-Fi status failure", EXPECT_FAIL);
    EXPECT_FATAL_WIFI_ERROR(WIFI_UNKNOWN_ERROR);

    RESET_MOCK_CONFIG();
    mock_ctx.inject.cyw43_auth_error_count = WIFI_BAD_AUTH_RETRY_COUNT;
    EXECUTE_TEST("Wi-Fi excess auth errors", EXPECT_FAIL);
    EXPECT_FATAL_WIFI_ERROR(WIFI_AUTH_ERROR);

    RESET_MOCK_CONFIG();
    mock_ctx.inject.cyw43_auth_error_count = WIFI_BAD_AUTH_RETRY_COUNT - 1;
    mock_ctx.inject.exit_on_ntp_success = 1;
    EXECUTE_TEST("Wi-Fi auth errors OK", EXPECT_OK);
    CHECK_ICONS_OK();

    RESET_MOCK_CONFIG();
    mock_ctx.inject.cyw43_auth_timeout_count = 99;
    EXECUTE_TEST("Wi-Fi excess timeout", EXPECT_FAIL);
    EXPECT_FATAL_WIFI_ERROR(WIFI_TIMEOUT_ERROR);

    RESET_MOCK_CONFIG();
    mock_ctx.inject.cyw43_auth_timeout_count = (WIFI_ABANDON_TIMEOUT_MS / WIFI_CONNECT_TIMEOUT_MS) - 1;
    mock_ctx.inject.exit_on_ntp_success = 1;
    EXECUTE_TEST("Wi-Fi OK timeout", EXPECT_OK);
    CHECK_ICONS_OK();

    return 0;
}

// Note: 'mo' is 0-indexed (2 = March, 9 = October, etc.)
#define TEST_DST_BOUND(yr, mo, dy, hr, mn, rule, expected)                                                             \
    do {                                                                                                               \
        clock_state->flash_config.dst_rule = rule;                                                                     \
        tm_val.tm_year = (yr) - 1900;                                                                                  \
        tm_val.tm_mon = (mo);                                                                                          \
        tm_val.tm_mday = (dy);                                                                                         \
        tm_val.tm_hour = (hr);                                                                                         \
        tm_val.tm_min = (mn);                                                                                          \
        tm_val.tm_sec = 0;                                                                                             \
        t = tm_to_epoch(&tm_val);                                                                                      \
        if (time_is_dst(t, clock_state) != (expected)) {                                                               \
            printf("DST Test Failed: %04d-%02d-%02d %02d:%02d\n", yr, mo, dy, hr, mn);                                 \
            return 1;                                                                                                  \
        }                                                                                                              \
    } while (0)

static int test_dst(void)
{
    repeating_timer_t timer;
    clock_state_t *clock_state = create_test_clock_state(&timer, create_flash_config());

    // Timezone Offset Tests (DST_RULE_NONE)`
    clock_state->ntp_last_sync = mock_time(NULL);
    clock_state->ntp_interval = NTP_SYNC_INTERVAL_SEC;

    // Test Positive Fractional Offset: India (+5:30 -> 330 mins)
    clock_state->flash_config.tz_offset_mins = 330;
    set_localtime(clock_state, 2024, 0, 1, 12, 0, 0); // Jan 1, 12:00 UTC
    (void)clock_timer_callback(&timer);
    clock_task(clock_state);
    EXPECT_LCD_DIGITS("Mon1730");
    CHECK_ICONS_OK();

    // Test Negative Offset: New York (-5:00 -> -300 mins)
    clock_state->flash_config.tz_offset_mins = -300;
    set_localtime(clock_state, 2024, 0, 1, 12, 0, 0); // Jan 1, 12:00 UTC
    (void)clock_timer_callback(&timer);
    clock_task(clock_state);
    EXPECT_LCD_DIGITS("Mon0700");
    CHECK_ICONS_OK();

    // Display Rollover Tests
    clock_state->flash_config.tz_offset_mins = 0; // Reset to UK base
    clock_state->flash_config.dst_rule = DST_RULE_EU;

    // Sun March 25, 2001 at 00:22 (just before EU clocks change)
    set_localtime(clock_state, 2001, 2, 25, 0, 22, 0);
    (void)clock_timer_callback(&timer);
    clock_task(clock_state);
    EXPECT_LCD_DIGITS("Sun0022");
    CHECK_ICONS_OK();

    // Sun March 25, 2001 at 01:22 (just after EU clocks change)
    set_localtime(clock_state, 2001, 2, 25, 1, 22, 0);
    (void)clock_timer_callback(&timer);
    clock_task(clock_state);
    EXPECT_LCD_DIGITS("Sun0222");
    CHECK_ICONS_OK();

    // Thu August 23, 2001 at 23:55 (test day rollover in DST)
    set_localtime(clock_state, 2001, 7, 23, 23, 55, 0);
    (void)clock_timer_callback(&timer);
    clock_task(clock_state);
    EXPECT_LCD_DIGITS("Fri0055");
    CHECK_ICONS_OK();

    const char *test_time = time_as_string(mock_time(NULL), clock_state);
    ASSERT_WITH_MESSAGE(strncmp(test_time, "00:55:00 (DST)", 12), 0, "Check time as string");

    // Exhaustive DST Boundary Math Tests
    struct tm tm_val = {0};
    time_t t;

    // --- Northern Hemisphere ---

    // NA: 2nd Sun Mar (02:00) to 1st Sun Nov (02:00) -> 2024: Mar 10, Nov 3
    TEST_DST_BOUND(2024, 2, 10, 1, 59, DST_RULE_NA, 0); // Before spring forward
    TEST_DST_BOUND(2024, 2, 10, 2, 0, DST_RULE_NA, 1);  // Spring forward triggers
    TEST_DST_BOUND(2024, 10, 3, 1, 59, DST_RULE_NA, 1); // Before fall back
    TEST_DST_BOUND(2024, 10, 3, 2, 0, DST_RULE_NA, 0);  // Fall back triggers

    // EU: Last Sun Mar (01:00) to Last Sun Oct (01:00) -> 2024: Mar 31, Oct 27
    TEST_DST_BOUND(2024, 2, 31, 0, 59, DST_RULE_EU, 0);
    TEST_DST_BOUND(2024, 2, 31, 1, 0, DST_RULE_EU, 1);
    TEST_DST_BOUND(2024, 9, 27, 0, 59, DST_RULE_EU, 1);
    TEST_DST_BOUND(2024, 9, 27, 1, 0, DST_RULE_EU, 0);

    // --- Southern Hemisphere (Wraps across New Year) ---

    // AU: 1st Sun Oct (02:00) to 1st Sun Apr (03:00) -> 2024: Oct 6, Apr 7
    TEST_DST_BOUND(2024, 9, 6, 1, 59, DST_RULE_AU, 0);   // Spring: Before Oct start
    TEST_DST_BOUND(2024, 9, 6, 2, 0, DST_RULE_AU, 1);    // Spring: DST starts
    TEST_DST_BOUND(2024, 11, 25, 12, 0, DST_RULE_AU, 1); // Peak Summer: Dec is DST!
    TEST_DST_BOUND(2024, 3, 7, 2, 59, DST_RULE_AU, 1);   // Autumn: Before Apr end
    TEST_DST_BOUND(2024, 3, 7, 3, 0, DST_RULE_AU, 0);    // Autumn: DST ends (Winter begins)
    TEST_DST_BOUND(2024, 6, 15, 12, 0, DST_RULE_AU, 0);  // Deep Winter: July is Standard Time

    // NZ: Last Sun Sep (02:00) to 1st Sun Apr (03:00) -> 2024: Sep 29, Apr 7
    TEST_DST_BOUND(2024, 8, 29, 1, 59, DST_RULE_NZ, 0); // Spring: Before Sep start
    TEST_DST_BOUND(2024, 8, 29, 2, 0, DST_RULE_NZ, 1);  // Spring: DST starts
    TEST_DST_BOUND(2024, 3, 7, 2, 59, DST_RULE_NZ, 1);  // Autumn: Before Apr end
    TEST_DST_BOUND(2024, 3, 7, 3, 0, DST_RULE_NZ, 0);   // Autumn: DST ends

    // --- No DST ---
    TEST_DST_BOUND(2024, 0, 15, 12, 0, DST_RULE_NONE, 0); // January 15th (Mid-winter/summer)
    TEST_DST_BOUND(2024, 5, 15, 12, 0, DST_RULE_NONE, 0); // June 15th (Mid-summer/winter)

    // --- Complex Edge Cases ---

    // Chile: 1st Sat Sep (24:00) to 1st Sat Apr (24:00) -> 2024: Sep 7, Apr 6
    // Note: 24:00 is mathematically 23:59:59 transition
    TEST_DST_BOUND(2024, 8, 7, 23, 58, DST_RULE_CL, 0);
    TEST_DST_BOUND(2024, 8, 7, 23, 59, DST_RULE_CL, 1);
    TEST_DST_BOUND(2024, 3, 6, 23, 58, DST_RULE_CL, 1);
    TEST_DST_BOUND(2024, 3, 6, 23, 59, DST_RULE_CL, 0);

    // Israel: Fri before last Sun Mar to Last Sun Oct -> 2024: Mar 29, Oct 27
    TEST_DST_BOUND(2024, 2, 29, 1, 59, DST_RULE_IL, 0);
    TEST_DST_BOUND(2024, 2, 29, 2, 0, DST_RULE_IL, 1);
    TEST_DST_BOUND(2024, 9, 27, 1, 59, DST_RULE_IL, 1);
    TEST_DST_BOUND(2024, 9, 27, 2, 0, DST_RULE_IL, 0);

    return 0; // All paths passed
}

static int lcd_digits_to_int(const char *digits)
{
    return ((*digits - '0') * 10) + (*(digits + 1) - '0');
}

static int test_clock_timer_paths(void)
{
    repeating_timer_t timer;
    clock_state_t *clock_state = create_test_clock_state(&timer, create_flash_config());

    RESET_MOCK_CONFIG();
    mock_ctx.inject.factory_reset_pressed = 1;
    ASSERT_WITH_MESSAGE(clock_timer_callback(&timer), true, "clock timer callback should keep running");
    ASSERT_WITH_MESSAGE(clock_state->clock_tick_updated, true, "clock tick should be marked updated");
    ASSERT_WITH_MESSAGE(clock_state->ap_mode_triggered, 0, "button hold should not trigger immediately");

    ASSERT_WITH_MESSAGE(clock_timer_callback(&timer), true, "second callback should keep running");
    ASSERT_WITH_MESSAGE(clock_timer_callback(&timer), true, "third callback should trigger the hold path");
    ASSERT_WITH_MESSAGE(clock_state->ap_mode_triggered, 1, "factory reset hold should trigger AP mode");

    mock_ctx.inject.factory_reset_pressed = 0;
    ASSERT_WITH_MESSAGE(clock_timer_callback(&timer), true, "released button should reset hold state");
    ASSERT_WITH_MESSAGE(clock_state->ap_mode_triggered, 1, "released button should keep previous trigger state");

    return 0;
}

static int test_clock_start_timer_failures(void)
{
    RESET_MOCK_CONFIG();
    mock_ctx.inject.fail_clock_timer_init = 1;
    EXECUTE_TEST("Clock timer init failure", EXPECT_FAIL);
    EXPECT_FATAL_NTP_ERROR(NTP_INIT_ERROR);

    RESET_MOCK_CONFIG();
    mock_ctx.inject.fail_backlight_timer_init = 1;
    EXECUTE_TEST("Backlight timer init failure", EXPECT_FAIL);
    EXPECT_FATAL_NTP_ERROR(NTP_INIT_ERROR);

    return 0;
}

static int test_ntp_time(void)
{
    repeating_timer_t timer;
    clock_state_t *clock_state = create_test_clock_state(&timer, create_flash_config());

    // Tue January 9, 2001 at 09:28:32
    set_localtime(clock_state, 2001, 0, 9, 9, 28, 32);

    // Run for 12 simulated days
    // +1d: normal NTP update
    // +2d: generate a KoD
    // +3d: should not update NTP
    // +4d: normal NTP update
    // +6d: create a DNS error
    // +7d: watchdog error should clear
    // +8d: normal NTP update (NTP error should clear)
    for (int day = 0; day <= 12; day++) {
        switch (day) {
            case 2:
                mock_ctx.inject.udp_response_type = UDP_NTP_KOD;
                break;
            case 3:
                mock_ctx.inject.udp_response_type = UDP_NTP_OK;
                break;
            case 6:
                mock_ctx.inject.dns_lookup_fail = 1;
                mock_ctx.inject.fatal_reset_no_longjmp = 1;
                clock_state->watchdog_reset_error = WATCHDOG_NTP;
                clock_state->last_watchdog_error_time =
                    (time_t)(mock_ctx.spy.system_time_ms / 1000) + NTP_SYNC_INTERVAL_SEC / 2;
                break;
            case 7:
                mock_ctx.inject.dns_lookup_fail = 0;
                break;
            default:
                break;
        }

        for (int second = 0; second < 24 * 60 * 60; second++) {
            sleep_ms(1000);

            time_t now = (time_t)(mock_ctx.spy.system_time_ms / 1000);
            struct tm *test_time = gmtime(&now);
            clock_task(clock_state);

            if (clock_state->current_lcd_digits[3]) {
                // Only check once the LCD has started getting time updates
                int lcd_hour = lcd_digits_to_int(&clock_state->current_lcd_digits[3]);
                int lcd_min = lcd_digits_to_int(&clock_state->current_lcd_digits[5]);

                if (test_time->tm_hour != lcd_hour || test_time->tm_min != lcd_min) {
                    test_printf("FAILED clock state: time=%02d:%02d, lcd=%02d:%02d\n", test_time->tm_hour,
                                test_time->tm_min, lcd_hour, lcd_min);
                }
            }

            mock_ctx.spy.ntp_seconds++;
        }

        switch (day) {
            case 1:
                ASSERT_WITH_MESSAGE(mock_ctx.spy.ntp_packet_sent, 1, "NTP updated");
                mock_ctx.spy.ntp_packet_sent = 0;
                break;
            case 2:
                ASSERT_WITH_MESSAGE(mock_ctx.spy.ntp_packet_sent, 1, "NTP updated");
                ASSERT_WITH_MESSAGE(clock_state->ntp_interval, NTP_SYNC_INTERVAL_SEC * 2, "Interval doubled via KoD");
                mock_ctx.spy.ntp_packet_sent = 0;
                break;
            case 3:
                ASSERT_WITH_MESSAGE(mock_ctx.spy.ntp_packet_sent, 0, "NTP not updated");
                break;
            case 6:
                ASSERT_WITH_MESSAGE(mock_ctx.spy.watchdog_icon, WATCHDOG_NTP, "Watchdog fired for NTP");
                break;
            case 7:
                ASSERT_WITH_MESSAGE(clock_state->watchdog_reset_error, WATCHDOG_OK, "watchdog cleared");
                ASSERT_WITH_MESSAGE(mock_ctx.spy.ntp_icon, NTP_DNS_ERROR, "NTP  OK");
                break;
            default:
                // CHECK_ICONS_OK();
                break;
        }

        // Simulate the Pico's hardware clock drifting from reality
        if (day == 7) {
            mock_ctx.spy.ntp_seconds += 100;
        }
    }

    mock_ctx.inject.udp_response_type = UDP_NTP_OK;

    // Thu February 7, 2036 at 06:28:59 (NTP Epoch 1)
    set_localtime(clock_state, 2036, 2, 7, 6, 28, 59);
    clock_state->ntp_last_sync = (time_t)(mock_ctx.spy.system_time_ms / 1000) - clock_state->ntp_interval;
    sleep_ms(1000);
    clock_task(clock_state);
    EXPECT_LCD_DIGITS("Fri0629");

    return 0;
}

static int test_ntp_unsynchronized_server(void)
{
    RESET_MOCK_CONFIG();
    mock_ctx.inject.udp_response_type = UDP_NTP_LEAP3;
    EXECUTE_TEST("NTP unsynchronized", EXPECT_FAIL);
    EXPECT_FATAL_NTP_ERROR(NTP_PROTOCOL_ERROR);
    return 0;
}

static int test_ntp_errors(void)
{
    RESET_MOCK_CONFIG();
    mock_ctx.inject.udp_response_type = UDP_NTP_INVALID;
    EXECUTE_TEST("NTP UDP invalid", EXPECT_FAIL);
    EXPECT_FATAL_NTP_ERROR(NTP_PROTOCOL_ERROR);

    RESET_MOCK_CONFIG();
    mock_ctx.inject.udp_response_type = UDP_NTP_BAD_LEN;
    EXECUTE_TEST("NTP UDP bad length failure", EXPECT_FAIL);
    EXPECT_FATAL_NTP_ERROR(NTP_PROTOCOL_ERROR);

    RESET_MOCK_CONFIG();
    mock_ctx.inject.udp_response_type = UDP_NTP_BAD_PORT;
    EXECUTE_TEST("NTP UDP bad port failure", EXPECT_FAIL);
    EXPECT_FATAL_NTP_ERROR(NTP_PROTOCOL_ERROR);

    RESET_MOCK_CONFIG();
    mock_ctx.inject.udp_new_ip_type_fail = 1;
    EXECUTE_TEST("NTP UDP new IP failure", EXPECT_FAIL);
    EXPECT_FATAL_NTP_ERROR(NTP_INIT_ERROR);

    RESET_MOCK_CONFIG();
    mock_ctx.inject.pbuf_alloc_fail_at = 1;
    EXECUTE_TEST("NTP pbuf alloc failure", EXPECT_FAIL);
    EXPECT_FATAL_NTP_ERROR(NTP_MEMORY_ERROR);

    RESET_MOCK_CONFIG();
    mock_ctx.inject.udp_sendto_fail = 1;
    EXECUTE_TEST("NTP sendto failure", EXPECT_FAIL);
    EXPECT_FATAL_NTP_ERROR(NTP_PROTOCOL_ERROR);

    RESET_MOCK_CONFIG();
    mock_ctx.inject.udp_invalid_addr = 1;
    EXECUTE_TEST("NTP invalid address", EXPECT_FAIL);
    EXPECT_FATAL_NTP_ERROR(NTP_DNS_ERROR);

    return 0;
}

static int test_watchdog(void)
{
    RESET_MOCK_CONFIG();
    mock_ctx.inject.exit_on_ntp_success = 1;
    EXECUTE_TEST("Watchdog init OK", EXPECT_OK);
    CHECK_ICONS_OK();

    RESET_MOCK_CONFIG();
    mock_ctx.inject.watchdog_caused_reboot = 1;
    mock_ctx.inject.exit_on_ntp_success = 1;
    EXECUTE_TEST("Watchdog reboot OK", EXPECT_OK);
    CHECK_WATCHDOG_RESET_OK();

    RESET_MOCK_CONFIG();
    mock_ctx.inject.watchdog_caused_reboot = 1;
    mock_ctx.inject.exit_on_ntp_success = 1;
    EXECUTE_TEST("Watchdog boot count", 0 || persistent_state.boot_count != 2);
    CHECK_WATCHDOG_RESET_OK();

    RESET_MOCK_CONFIG();
    mock_ctx.inject.cyw43_arch_init_fail = 1;
    EXECUTE_TEST("Watchdog reboot on Wi-Fi", 1 || !mock_ctx.spy.watchdog_reboot_called);
    EXPECT_FATAL_WIFI_ERROR(WIFI_INIT_ERROR);

    RESET_MOCK_CONFIG();
    mock_ctx.inject.dns_lookup_fail = 1;
    EXECUTE_TEST("Watchdog reboot on DNS", 1 || !mock_ctx.spy.watchdog_reboot_called);
    EXPECT_FATAL_NTP_ERROR(NTP_DNS_ERROR);

    RESET_MOCK_CONFIG();
    mock_ctx.inject.watchdog_caused_reboot = 1;
    mock_ctx.inject.exit_on_ntp_success = 1;
    EXECUTE_TEST("Watchdog DNS OK", EXPECT_OK);
    CHECK_WATCHDOG_RESET_OK();

    return 0;
}

static int test_error_strings(void)
{
    ASSERT_WITH_MESSAGE(strcmp(wifi_error_to_string(WIFI_OK), "WIFI_OK"), 0, "Wi-Fi status string");
    ASSERT_WITH_MESSAGE(strcmp(wifi_error_to_string(WIFI_INIT_ERROR), "WIFI_INIT_ERROR"), 0, "Wi-Fi status string");
    ASSERT_WITH_MESSAGE(strcmp(wifi_error_to_string(WIFI_TIMEOUT_ERROR), "WIFI_TIMEOUT_ERROR"), 0,
                        "Wi-Fi status string");
    ASSERT_WITH_MESSAGE(strcmp(wifi_error_to_string(WIFI_AUTH_ERROR), "WIFI_AUTH_ERROR"), 0, "Wi-Fi status string");
    ASSERT_WITH_MESSAGE(strcmp(wifi_error_to_string(WIFI_CONNECT_ERROR), "WIFI_CONNECT_ERROR"), 0,
                        "Wi-Fi status string");
    ASSERT_WITH_MESSAGE(strcmp(wifi_error_to_string(WIFI_UNKNOWN_ERROR), "WIFI_UNKNOWN_ERROR"), 0,
                        "Wi-Fi status string");

    ASSERT_WITH_MESSAGE(strcmp(ntp_error_to_string(NTP_OK), "NTP_OK"), 0, "NTP status string");
    ASSERT_WITH_MESSAGE(strcmp(ntp_error_to_string(NTP_INIT_ERROR), "NTP_INIT_ERROR"), 0, "NTP status string");
    ASSERT_WITH_MESSAGE(strcmp(ntp_error_to_string(NTP_DNS_ERROR), "NTP_DNS_ERROR"), 0, "NTP status string");
    ASSERT_WITH_MESSAGE(strcmp(ntp_error_to_string(NTP_TIMEOUT_ERROR), "NTP_TIMEOUT_ERROR"), 0, "NTP status string");
    ASSERT_WITH_MESSAGE(strcmp(ntp_error_to_string(NTP_PROTOCOL_ERROR), "NTP_PROTOCOL_ERROR"), 0, "NTP status string");
    ASSERT_WITH_MESSAGE(strcmp(ntp_error_to_string(NTP_MEMORY_ERROR), "NTP_MEMORY_ERROR"), 0, "NTP status string");
    ASSERT_WITH_MESSAGE(strcmp(ntp_error_to_string(NTP_NULL_ERROR), "NTP_NULL_ERROR"), 0, "NTP status string");

    ASSERT_WITH_MESSAGE(strcmp(watchdog_error_to_string(WATCHDOG_OK), "WATCHDOG_OK"), 0, "Watchdog status string");
    ASSERT_WITH_MESSAGE(strcmp(watchdog_error_to_string(WATCHDOG_RESET), "WATCHDOG_RESET"), 0,
                        "Watchdog status string");
    ASSERT_WITH_MESSAGE(strcmp(watchdog_error_to_string(WATCHDOG_NTP), "WATCHDOG_NTP"), 0, "Watchdog status string");
    ASSERT_WITH_MESSAGE(strcmp(watchdog_error_to_string(WATCHDOG_WIFI), "WATCHDOG_WIFI"), 0, "Watchdog status string");

    // Coverage on otherwise invalid status debug values
    if ((strcmp(watchdog_error_to_string((watchdog_error_t)0xff), "UNKNOWN_STATUS") != 0) ||
        (strcmp(wifi_error_to_string((wifi_error_t)0xff), "UNKNOWN_STATUS") != 0) ||
        (strcmp(ntp_error_to_string((ntp_error_t)0xff), "UNKNOWN_STATUS") != 0)) {
        return 1;
    }
    return 0;
}

static char *dst_rule_str[] = {
    "NONE", /* DST_RULE_NONE */
    "NA",   /* DST_RULE_NA */
    "EU",   /* DST_RULE_EU */
    "AU",   /* DST_RULE_AU */
    "NZ",   /* DST_RULE_NZ */
    "CL",   /* DST_RULE_CL */
    "IL",   /* DST_RULE_IL */
};

static char *config_post_url(const char *ssid, const char *pwd, const char *ntp, int16_t tz, dst_rule_t dst,
                             uint32_t cto, uint16_t port)
{
    static char body[2000];
    static char payload[2048];

    size_t max_len = sizeof(body) - 1;
    char *body_ptr = body;
    if (ssid) {
        int len = snprintf(body_ptr, max_len, "&ssid=%s", ssid);
        body_ptr += len;
        max_len -= (size_t)len;
    }
    if (pwd) {
        int len = snprintf(body_ptr, max_len, "&pwd=%s", pwd);
        body_ptr += len;
        max_len -= (size_t)len;
    }
    if (ntp) {
        int len = snprintf(body_ptr, max_len, "&ntp=%s", ntp);
        body_ptr += len;
        max_len -= (size_t)len;
    }
    if (tz) {
        int len = snprintf(body_ptr, max_len, "&tz=%d", tz);
        body_ptr += len;
        max_len -= (size_t)len;
    }
    if (dst) {
        char *dst_str = dst_rule_str[dst % 7];
        int len = snprintf(body_ptr, max_len, "&dst=%s", dst_str);
        body_ptr += len;
        max_len -= (size_t)len;
    }
    if (cto) {
        int len = snprintf(body_ptr, max_len, "&cto=%u", cto);
        body_ptr += len;
        max_len -= (size_t)len;
    }
    if (port) {
        int len = snprintf(body_ptr, max_len, "&port=%d", port);
        body_ptr += len;
        max_len -= (size_t)len;
    }
    if (body[0] == '&')
        body_ptr = body + 1;
    else
        body_ptr = body;
    size_t content_length = strlen(body_ptr);
    snprintf(payload, sizeof(payload), "POST / HTTP/1.1\r\nContent-Length: %d\r\n\r\n%s", (int)content_length,
             body_ptr);
    return (char *)payload;
}

// ============================================================================
// Wi-Fi & AP TCP-IP Mock Config & State
// ============================================================================

static int config_save_count = 0;

static struct flash_config_t last_config;
static bool mock_store_config_success(struct flash_config_t *config, bool invalidate)
{
    (void)invalidate;
    config_save_count++;
    last_config = *config;
    return true; // Return success
}

static bool mock_store_config_fail_then_success(struct flash_config_t *config, bool invalidate)
{
    (void)invalidate;
    config_save_count++;
    if (config_save_count == 1) {
        return false;
    }
    last_config = *config;
    return true;
}

static void reset_wifi_test_state(void)
{
    RESET_MOCK_CONFIG();
    config_save_count = 0;
    memset(&last_config, 0, sizeof(last_config));
    mock_clear_tcp_payloads();
}

// ============================================================================
// Access Point (AP) & TCP Server Tests
// ============================================================================

static int test_wifi_tcp_callback_paths(void)
{
    RESET_MOCK_CONFIG();

    tcp_server_t server = {0};
    struct tcp_pcb client = {0};
    err_t result = tcp_server_accept(&server, &client, ERR_OK);
    ASSERT_WITH_MESSAGE(result, ERR_OK, "accept should succeed for a fresh connection");

    ASSERT_WITH_MESSAGE(mock_ctx.sim.tcp_poll_cb != NULL, 1, "poll callback should be registered");
    ASSERT_WITH_MESSAGE(mock_ctx.sim.tcp_sent_cb != NULL, 1, "sent callback should be registered");
    ASSERT_WITH_MESSAGE(mock_ctx.sim.tcp_err_cb != NULL, 1, "error callback should be registered");

    mock_ctx.sim.tcp_poll_cb(mock_ctx.sim.conn_arg, &mock_ctx.sim.conn_pcb);
    ASSERT_WITH_MESSAGE(server.active_connections, 0, "poll callback should close and release the connection");

    RESET_MOCK_CONFIG();
    server = (tcp_server_t){0};
    result = tcp_server_accept(&server, &client, ERR_OK);
    ASSERT_WITH_MESSAGE(result, ERR_OK, "accept should succeed for the second pass");

    mock_ctx.inject.tcp_close_fail = 1;
    mock_ctx.sim.tcp_sent_cb(mock_ctx.sim.conn_arg, &mock_ctx.sim.conn_pcb, 1);
    ASSERT_WITH_MESSAGE(server.active_connections, 0, "sent callback should still clean up when tcp_close fails");

    RESET_MOCK_CONFIG();
    server = (tcp_server_t){0};
    result = tcp_server_accept(&server, NULL, ERR_OK);
    ASSERT_WITH_MESSAGE(result, ERR_VAL, "accept should reject a null PCB");

    result = tcp_server_accept(&server, &client, ERR_VAL);
    ASSERT_WITH_MESSAGE(result, ERR_VAL, "accept should reject a non-OK accept error");

    for (int i = 0; i < TCP_IP_MAX_CONNECTIONS; i++) {
        server.connections[i].pcb = &client;
    }
    result = tcp_server_accept(&server, &client, ERR_OK);
    ASSERT_WITH_MESSAGE(result, ERR_MEM, "accept should reject when no connection slots are free");

    return 0;
}

static int test_wifi_startup_failures(void)
{
    RESET_MOCK_CONFIG();
    mock_ctx.inject.tcp_bind_fail = 1;
    bool wifi_initialized = false;
    wifi_error_t err = start_wifi_access_point(NULL, mock_store_config_success, &wifi_initialized);
    ASSERT_WITH_MESSAGE(err, WIFI_INIT_ERROR, "AP startup should fail when TCP bind fails");

    RESET_MOCK_CONFIG();
    mock_ctx.inject.tcp_listen_fail = 1;
    wifi_initialized = false;
    err = start_wifi_access_point(NULL, mock_store_config_success, &wifi_initialized);
    ASSERT_WITH_MESSAGE(err, WIFI_INIT_ERROR, "AP startup should fail when TCP listen fails");

    return 0;
}

static int test_wifi_request_parser_paths(void)
{
    RESET_MOCK_CONFIG();

    tcp_connect_state_t con_state = {0};
    struct pbuf p = {0};
    err_t result = tcp_server_recv(&con_state, NULL, NULL, ERR_OK);
    ASSERT_WITH_MESSAGE(result, ERR_OK, "recv should close cleanly on null pbuf");

    con_state = (tcp_connect_state_t){0};
    p.tot_len = 0;
    p.len = 0;
    result = tcp_server_recv(&con_state, NULL, &p, ERR_OK);
    ASSERT_WITH_MESSAGE(result, ERR_OK, "recv should handle empty pbufs");

    con_state = (tcp_connect_state_t){0};
    const char *bad_len = "POST / HTTP/1.1\r\nContent-Length: \r\n\r\nbody";
    strncpy((char *)p.payload, bad_len, sizeof(p.payload) - 1);
    p.tot_len = (u16_t)strlen(bad_len);
    p.len = p.tot_len;
    result = tcp_server_recv(&con_state, NULL, &p, ERR_OK);
    ASSERT_WITH_MESSAGE(result, ERR_VAL, "recv should reject malformed content length headers");

    con_state = (tcp_connect_state_t){0};
    const char *invalid_num = "POST / HTTP/1.1\r\nContent-Length: abc\r\n\r\nbody";
    strncpy((char *)p.payload, invalid_num, sizeof(p.payload) - 1);
    p.tot_len = (u16_t)strlen(invalid_num);
    p.len = p.tot_len;
    result = tcp_server_recv(&con_state, NULL, &p, ERR_OK);
    ASSERT_WITH_MESSAGE(result, ERR_VAL, "recv should reject non-numeric content lengths");

    con_state = (tcp_connect_state_t){0};
    const char *incomplete = "POST / HTTP/1.1\r\nContent-Length: 10\r\n\r\nshort";
    strncpy((char *)p.payload, incomplete, sizeof(p.payload) - 1);
    p.tot_len = (u16_t)strlen(incomplete);
    p.len = p.tot_len;
    result = tcp_server_recv(&con_state, NULL, &p, ERR_OK);
    ASSERT_WITH_MESSAGE(result, ERR_OK, "recv should wait on incomplete POST bodies");

    con_state = (tcp_connect_state_t){0};
    con_state.store_config = mock_store_config_success;
    const char *bad_req = "POST / HTTP/1.1\r\nContent-Length: 5\r\n\r\ncto=0";
    strncpy((char *)p.payload, bad_req, sizeof(p.payload) - 1);
    p.tot_len = (u16_t)strlen(bad_req);
    p.len = p.tot_len;
    result = tcp_server_recv(&con_state, NULL, &p, ERR_OK);
    ASSERT_WITH_MESSAGE(result, ERR_OK, "recv should return OK after handling a bad request");
    ASSERT_WITH_MESSAGE(strstr(mock_ctx.sim.tcp_write_buffer, "400 Bad Request") != NULL, 1,
                        "recv should write a 400 response for invalid config values");

    tcp_server_t server = {0};
    struct tcp_pcb client = {0};
    err_t accept_result = tcp_server_accept(&server, &client, ERR_OK);
    ASSERT_WITH_MESSAGE(accept_result, ERR_OK, "accept should register the TCP callbacks");

    con_state = (tcp_connect_state_t){0};
    con_state.header_len = 4;
    con_state.result_len = 4;
    con_state.sent_len = 1;
    mock_ctx.sim.tcp_sent_cb(mock_ctx.sim.conn_arg, &mock_ctx.sim.conn_pcb, 1);
    ASSERT_WITH_MESSAGE(mock_ctx.sim.tcp_sent_pending, 0,
                        "sent callback should not queue extra sends before completion");

    RESET_MOCK_CONFIG();
    server = (tcp_server_t){0};
    accept_result = tcp_server_accept(&server, &client, ERR_OK);
    ASSERT_WITH_MESSAGE(accept_result, ERR_OK, "accept should register a fresh sent callback");

    con_state = (tcp_connect_state_t){0};
    con_state.header_len = 4;
    con_state.result_len = 4;
    con_state.sent_len = 8;
    mock_ctx.sim.tcp_sent_cb(mock_ctx.sim.conn_arg, &mock_ctx.sim.conn_pcb, 1);
    ASSERT_WITH_MESSAGE(mock_ctx.sim.tcp_sent_pending, 0,
                        "sent callback should complete and close the connection after transfer");

    RESET_MOCK_CONFIG();
    server = (tcp_server_t){0};
    accept_result = tcp_server_accept(&server, &client, ERR_OK);
    ASSERT_WITH_MESSAGE(accept_result, ERR_OK, "accept should register the poll callback");
    ASSERT_WITH_MESSAGE(mock_ctx.sim.tcp_poll_cb != NULL, 1, "poll callback should be available");
    ASSERT_WITH_MESSAGE(mock_ctx.sim.conn_arg != NULL, 1, "poll callback should have a connection state");
    mock_ctx.sim.tcp_poll_cb(mock_ctx.sim.conn_arg, &mock_ctx.sim.conn_pcb);
    ASSERT_WITH_MESSAGE(server.active_connections, 0, "poll callback should close the connection");

    RESET_MOCK_CONFIG();
    server = (tcp_server_t){0};
    accept_result = tcp_server_accept(&server, &client, ERR_OK);
    ASSERT_WITH_MESSAGE(accept_result, ERR_OK, "accept should register the error callback");
    ASSERT_WITH_MESSAGE(mock_ctx.sim.tcp_err_cb != NULL, 1, "error callback should be available");
    ASSERT_WITH_MESSAGE(mock_ctx.sim.conn_arg != NULL, 1, "error callback should have a connection state");
    mock_ctx.sim.tcp_err_cb(mock_ctx.sim.conn_arg, ERR_RST);
    ASSERT_WITH_MESSAGE(server.active_connections, 0, "error callback should close the connection");

    return 0;
}

static int test_wifi_config_urls(void)
{

    reset_wifi_test_state();
    mock_queue_tcp_payload(config_post_url(TEST_AP_SSID, TEST_AP_PASSWORD, TEST_NTP_SERVER, TEST_TZ_OFFSET,
                                           TEST_DST_RULE, TEST_TIMEOUT, TEST_NTP_PORT));
    clock_state_t state = {.wifi_initialized = false};
    wifi_error_t err = start_wifi_access_point(NULL, mock_store_config_success, &state.wifi_initialized);
    ASSERT_WITH_MESSAGE(err, WIFI_OK, "AP should start successfully");
    ASSERT_WITH_MESSAGE(strcmp(last_config.wifi_ssid, TEST_AP_SSID), 0, "URL decode SSID");
    ASSERT_WITH_MESSAGE(strcmp(last_config.wifi_password, TEST_AP_PASSWORD), 0, "URL decode password");
    ASSERT_WITH_MESSAGE(strcmp(last_config.ntp_server, TEST_NTP_SERVER), 0, "URL NTP server");
    ASSERT_WITH_MESSAGE(last_config.tz_offset_mins, TEST_TZ_OFFSET, "URL TZ offset");
    ASSERT_WITH_MESSAGE(last_config.ntp_timeout, TEST_TIMEOUT, "URL timeout");
    ASSERT_WITH_MESSAGE(last_config.dst_rule, TEST_DST_RULE, "URL DST rule");
    ASSERT_WITH_MESSAGE(last_config.ntp_port, TEST_NTP_PORT, "URL decode NTP port");

    // Stress URL decode
    // ssid: "My Wi-Fi!" (Testing + and %21)
    // pwd:  "a&b=c%d"   (Testing %26, %3D, %25)
    // Newlines should be removed from the password.
    static char url[256];
    static char body[] = "ssid=My+Wi-Fi%21&pwd=a%26b%3Dc%25d\r\n";
    snprintf(url, sizeof(url), "POST / HTTP/1.1\r\nContent-Length: %d\r\n\r\n%s", (int)sizeof(body) - 1, body);
    reset_wifi_test_state();
    mock_queue_tcp_payload(url);
    err = start_wifi_access_point(NULL, mock_store_config_success, &state.wifi_initialized);
    ASSERT_WITH_MESSAGE(err, WIFI_OK, "AP should start successfully");
    ASSERT_WITH_MESSAGE(strcmp(last_config.wifi_ssid, "My Wi-Fi!"), 0, "URL decode SSID stress");
    ASSERT_WITH_MESSAGE(strcmp(last_config.wifi_password, "a&b=c%d"), 0, "URL decode password stress");

    // Buffer overflow tests
    reset_wifi_test_state();
    mock_queue_tcp_payload(
        config_post_url("1234567890123456789012345678901234567890",                               // 40 chars
                        "1234567890123456789012345678901234567890123456789012345678901234567890", // 70 chars
                        NULL, 0, DST_RULE_NONE, 0, 0));

    start_wifi_access_point(NULL, mock_store_config_success, &state.wifi_initialized);
    // Assert strictly null-terminated and truncated correctly
    ASSERT_WITH_MESSAGE(strlen(last_config.wifi_ssid) > WIFI_SSID_MAX_LEN, 0, "Max SSID length");
    ASSERT_WITH_MESSAGE(strlen(last_config.wifi_password) > WIFI_PASSWORD_MAX_LEN, 0, "Max password length");
    ASSERT_WITH_MESSAGE(strncmp(last_config.wifi_ssid, "12345678901234567890123456789012", WIFI_SSID_MAX_LEN), 0,
                        "Max SSID consumed");

    reset_wifi_test_state();
    mock_queue_tcp_payload(config_post_url(NULL, NULL, NULL, 0, DST_RULE_EU, 0, 0));
    start_wifi_access_point(NULL, mock_store_config_success, &state.wifi_initialized);
    ASSERT_WITH_MESSAGE(last_config.dst_rule, DST_RULE_EU, "EU DST config");

    reset_wifi_test_state();
    mock_queue_tcp_payload(config_post_url(NULL, NULL, NULL, 0, DST_RULE_AU, 0, 0));
    start_wifi_access_point(NULL, mock_store_config_success, &state.wifi_initialized);
    ASSERT_WITH_MESSAGE(last_config.dst_rule, DST_RULE_AU, "AU DST config");

    reset_wifi_test_state();
    mock_queue_tcp_payload(config_post_url(NULL, NULL, NULL, 0, DST_RULE_NZ, 0, 0));
    start_wifi_access_point(NULL, mock_store_config_success, &state.wifi_initialized);
    ASSERT_WITH_MESSAGE(last_config.dst_rule, DST_RULE_NZ, "NZ DST config");

    reset_wifi_test_state();
    mock_queue_tcp_payload(config_post_url(NULL, NULL, NULL, 0, DST_RULE_CL, 0, 0));
    start_wifi_access_point(NULL, mock_store_config_success, &state.wifi_initialized);
    ASSERT_WITH_MESSAGE(last_config.dst_rule, DST_RULE_CL, "CL DST config");

    reset_wifi_test_state();
    mock_queue_tcp_payload(config_post_url(NULL, NULL, NULL, 0, DST_RULE_IL, 0, 0));
    start_wifi_access_point(NULL, mock_store_config_success, &state.wifi_initialized);
    ASSERT_WITH_MESSAGE(last_config.dst_rule, DST_RULE_IL, "IL DST config");

    reset_wifi_test_state();
    mock_queue_tcp_payload("POST / HTTP/1.1\r\nContent-Length: 8\r\n\r\nled_on=1");
    start_wifi_access_point(NULL, mock_store_config_success, &state.wifi_initialized);
    ASSERT_WITH_MESSAGE(last_config.led_always_on, true, "LED enable");

    reset_wifi_test_state();
    mock_queue_tcp_payload("POST / HTTP/1.1\r\nContent-Length: 8\r\n\r\nled_on=0");
    start_wifi_access_point(NULL, mock_store_config_success, &state.wifi_initialized);
    ASSERT_WITH_MESSAGE(last_config.led_always_on, false, "LED disable");

    // reset_wifi_test_state();
    // mock_queue_tcp_payload("POST / HTTP/1.1\r\nContent-Length: 7\r\n\r\ndst=bad");
    // start_wifi_access_point(NULL, mock_store_config_success, &state.wifi_initialized);
    // ASSERT_WITH_MESSAGE(last_config.dst_rule, DST_RULE_NONE, "invalid DST config");

    return 0;
}

static int test_wifi_ap_limits(void)
{
    // 1. Initialize the mock server state
    tcp_server_t mock_server = {0};

    // 2. Simulate 5 parallel TCP handshakes from a smartphone browser
    struct tcp_pcb mock_pcbs[TCP_IP_MAX_CONNECTIONS];
    int accepted_count = 0;
    int rejected_count = 0;

    for (int i = 0; i < TCP_IP_MAX_CONNECTIONS + 2; i++) {
        err_t result = tcp_server_accept(&mock_server, &mock_pcbs[i], ERR_OK);
        if (result == ERR_OK) {
            accepted_count++;
        } else if (result == ERR_ABRT) {
            rejected_count++;
        }
    }

    // Assert that the gatekeeper protected the heap
    ASSERT_WITH_MESSAGE(accepted_count, TCP_IP_MAX_CONNECTIONS, "Gatekeeper failed: allowed too many connections!");
    ASSERT_WITH_MESSAGE(rejected_count, 2, "Gatekeeper failed: did not abort excess connections!");

    // Send data in chunks
    tcp_connect_state_t con_state = {0};
    struct pbuf p1 = {0};
    char chunk1[256];
    snprintf(chunk1, sizeof(chunk1),
             "POST / HTTP/1.1\r\n"
             "Content-Length: %d\r\n"
             "\r\n"
             "ssid=Overflow&pad=",
             TCP_IP_BUFFER_SIZE + 1000);

    memcpy(&p1.payload, chunk1, sizeof(chunk1));
    p1.tot_len = (u16_t)sizeof(chunk1);
    p1.len = p1.tot_len;

    err_t res1 = tcp_server_recv(&con_state, NULL, &p1, ERR_OK);

    ASSERT_WITH_MESSAGE(res1, ERR_OK, "Chunk 1 should return ERR_OK (waiting for more data)");
    ASSERT_WITH_MESSAGE(strlen(con_state.headers), strlen(chunk1), "Chunk 1 copied to buffer");

    struct pbuf p2 = {0};
    char chunk2[TCP_IP_BUFFER_SIZE];
    memset(chunk2, 'A', sizeof(chunk2)); // Fill with 'A's

    memcpy(&p2.payload, chunk2, sizeof(chunk2));
    p2.tot_len = (u16_t)sizeof(chunk2);
    p2.len = p2.tot_len;

    err_t res2 = tcp_server_recv(&con_state, NULL, &p2, ERR_OK);

    // 4. Verify the protections worked
    ASSERT_WITH_MESSAGE(res2, ERR_OK, "Chunk 2 returns ERR_OK");

    // Ensure we didn't exceed the buffer size (leaving 1 byte for the null terminator)
    ASSERT_WITH_MESSAGE(strlen(con_state.headers), TCP_IP_BUFFER_SIZE - 1,
                        "Buffer should cap exactly at TCP_IP_BUFFER_SIZE - 1");

    // Ensure the truncation actually captured the 'A's from the second chunk
    ASSERT_WITH_MESSAGE(con_state.headers[TCP_IP_BUFFER_SIZE - 2], 'A',
                        "Buffer should end with the truncated data from Chunk 2");

    return 0;
}

static int test_ap_init_fails_cyw43(void)
{
    reset_wifi_test_state();
    mock_ctx.inject.cyw43_arch_init_fail = 1;
    clock_state_t state = {.wifi_initialized = false};

    wifi_error_t err = start_wifi_access_point(NULL, mock_store_config_success, &state.wifi_initialized);
    ASSERT_WITH_MESSAGE(err, WIFI_INIT_ERROR, "Should fail when CYW43 init fails");
    return 0;
}

static int test_ap_wifi_already_initialized(void)
{
    reset_wifi_test_state();
    mock_queue_tcp_payload("POST / HTTP/1.1\r\nContent-Length: 10\r\n\r\nssid=Hello");

    clock_state_t state = {.wifi_initialized = true};

    // If it attempts to initialize cyw43 again, it would fail.
    // This verifies the short-circuit logic works.
    mock_ctx.inject.cyw43_arch_init_fail = 1;

    wifi_error_t err = start_wifi_access_point(NULL, mock_store_config_success, &state.wifi_initialized);
    ASSERT_WITH_MESSAGE(err, WIFI_OK, "Should bypass init if already initialized");
    return 0;
}

static int test_ap_success_full_post(void)
{
    reset_wifi_test_state();
    const char *post_req = "POST / HTTP/1.1\r\n"
                           "Content-Length: 75\r\n"
                           "\r\n"
                           "ssid=MyNetwork&pwd=MyPassword&ntp=pool.ntp.org&tz=-420&dst=NA&cto=5000&port=123";

    mock_queue_tcp_payload(post_req);

    clock_state_t state = {.wifi_initialized = false};
    wifi_error_t err = start_wifi_access_point(NULL, mock_store_config_success, &state.wifi_initialized);

    ASSERT_WITH_MESSAGE(err, WIFI_OK, "AP should start successfully");
    ASSERT_WITH_MESSAGE(config_save_count, 1, "Config should be stored exactly once");
    ASSERT_WITH_MESSAGE(strcmp(last_config.wifi_ssid, "MyNetwork"), 0, "SSID string parsing failed");
    ASSERT_WITH_MESSAGE(strcmp(last_config.wifi_password, "MyPassword"), 0, "Password string parsing failed");
    ASSERT_WITH_MESSAGE(strcmp(last_config.ntp_server, "pool.ntp.org"), 0, "NTP string parsing failed");
    ASSERT_WITH_MESSAGE(last_config.tz_offset_mins, -420, "Timezone integer cast failed");
    ASSERT_WITH_MESSAGE(last_config.dst_rule, DST_RULE_NA, "DST rule mapping failed");
    ASSERT_WITH_MESSAGE(last_config.ntp_timeout, 5000, "Timeout integer cast failed");
    ASSERT_WITH_MESSAGE(last_config.ntp_port, 123, "Port integer cast failed");

    return 0;
}

static int test_ap_reuse_config(void)
{
    struct flash_config_t flash_config = {
        .wifi_ssid = "OldNet",
        .wifi_password = "s3cr3t",
        .ntp_server = "ntp.example.org",
    };
    reset_wifi_test_state();
    mock_queue_tcp_payload("POST / HTTP/1.1\r\nContent-Length: 9\r\n\r\nport=1234");

    clock_state_t state = {.wifi_initialized = false};
    start_wifi_access_point(&flash_config, mock_store_config_success, &state.wifi_initialized);

    ASSERT_WITH_MESSAGE(config_save_count, 1, "Config should be stored exactly once");
    ASSERT_WITH_MESSAGE(strcmp(last_config.wifi_ssid, "OldNet"), 0, "SSID string parsing failed");
    ASSERT_WITH_MESSAGE(strcmp(last_config.wifi_password, "s3cr3t"), 0, "Password string parsing failed");
    ASSERT_WITH_MESSAGE(strcmp(last_config.ntp_server, "ntp.example.org"), 0, "NTP string parsing failed");
    ASSERT_WITH_MESSAGE(last_config.ntp_port, 1234, "Port integer cast failed");

    return 0;
}

static int test_ap_url_decoding(void)
{
    reset_wifi_test_state();

    // The + should decode to a space, %20 should decode to a space, %2E to a dot
    const char *post_req = "POST / HTTP/1.1\r\n"
                           "Content-Length: 46\r\n"
                           "\r\n"
                           "ssid=My+Network&pwd=My%20Password&ntp=a%2Eb.com";

    mock_queue_tcp_payload(post_req);

    clock_state_t state = {.wifi_initialized = false};
    wifi_error_t err = start_wifi_access_point(NULL, mock_store_config_success, &state.wifi_initialized);

    ASSERT_WITH_MESSAGE(err, WIFI_OK, "AP should handle decoding successfully");
    ASSERT_WITH_MESSAGE(strcmp(last_config.wifi_ssid, "My Network"), 0, "Failed to decode + as space");
    ASSERT_WITH_MESSAGE(strcmp(last_config.wifi_password, "My Password"), 0, "Failed to decode %20 as space");
    ASSERT_WITH_MESSAGE(strcmp(last_config.ntp_server, "a.b.com"), 0, "Failed to decode %2E as dot");

    return 0;
}

static int test_ap_url_decode_malformed(void)
{
    reset_wifi_test_state();
    // %ZZ is invalid hex. `hex_to_int` returns 0, terminating the string early.
    mock_queue_tcp_payload("POST / HTTP/1.1\r\nContent-Length: 12\r\n\r\nssid=Abc%ZZd");

    clock_state_t state = {.wifi_initialized = false};
    wifi_error_t err = start_wifi_access_point(NULL, mock_store_config_success, &state.wifi_initialized);

    ASSERT_WITH_MESSAGE(err, WIFI_OK, "AP should handle malformed hex strings");
    ASSERT_WITH_MESSAGE(strcmp(last_config.wifi_ssid, "Abc"), 0, "Should terminate safely at invalid hex");

    return 0;
}

static int test_ap_dst_rule_fallback(void)
{
    reset_wifi_test_state();
    // Providing an unknown DST rule string should fall back to DST_RULE_NONE
    mock_queue_tcp_payload("POST / HTTP/1.1\r\nContent-Length: 14\r\n\r\nssid=A&dst=FOO");
    clock_state_t state = {.wifi_initialized = false};
    wifi_error_t err = start_wifi_access_point(NULL, mock_store_config_success, &state.wifi_initialized);

    ASSERT_WITH_MESSAGE(err, WIFI_OK, "AP should handle unknown DST gracefully");
    ASSERT_WITH_MESSAGE(last_config.dst_rule, DST_RULE_NONE, "Should fallback to DST_RULE_NONE");

    return 0;
}

static int test_ap_get_config_page(void)
{
    reset_wifi_test_state();

    mock_queue_tcp_payload("GET /invalid HTTP/1.1\r\n\r\n");
    mock_queue_tcp_payload("GET /clock-config HTTP/1.1\r\n\r\n");
    mock_queue_tcp_payload("POST / HTTP/1.1\r\nContent-Length: 9\r\n\r\nssid=Exit");

    clock_state_t state = {.wifi_initialized = false};
    wifi_error_t err = start_wifi_access_point(NULL, mock_store_config_success, &state.wifi_initialized);

    ASSERT_WITH_MESSAGE(err, WIFI_OK, "Should survive GET request and exit on POST");
    return 0;
}

static int test_ap_get_redirect(void)
{
    reset_wifi_test_state();

    // 1. GET request for unknown page (Route C - Captive Portal Redirect)
    mock_queue_tcp_payload("GET /generate_204 HTTP/1.1\r\n\r\n");
    // 2. Queue valid POST to exit loop
    mock_queue_tcp_payload("POST / HTTP/1.1\r\nContent-Length: 9\r\n\r\nssid=Exit");

    clock_state_t state = {.wifi_initialized = false};
    wifi_error_t err = start_wifi_access_point(NULL, mock_store_config_success, &state.wifi_initialized);

    ASSERT_WITH_MESSAGE(err, WIFI_OK, "Should survive redirect request and exit on POST");
    return 0;
}

static int test_ap_post_save_fails(void)
{
    reset_wifi_test_state();

    // 1. Valid POST, but we will mock a Flash write failure
    mock_queue_tcp_payload("POST / HTTP/1.1\r\nContent-Length: 9\r\n\r\nssid=Fail");
    // 2. Second attempt succeeds
    mock_queue_tcp_payload("POST / HTTP/1.1\r\nContent-Length: 9\r\n\r\nssid=Pass");

    clock_state_t state = {.wifi_initialized = false};
    wifi_error_t err = start_wifi_access_point(NULL, mock_store_config_fail_then_success, &state.wifi_initialized);

    ASSERT_WITH_MESSAGE(err, WIFI_OK, "Should recover from a failed config store");
    ASSERT_WITH_MESSAGE(config_save_count, 2, "Store config should have been called twice");
    // ASSERT_WITH_MESSAGE(strcmp(last_config.wifi_ssid, "Pass"), 0, "Last config stored should be the passing
    // one");

    return 0;
}

static int test_ap_incomplete_requests(void)
{
    reset_wifi_test_state();

    // 1. Missing double \r\n boundary (Headers incomplete)
    mock_queue_tcp_payload("GET / HTTP/1.1");
    // 2. POST with missing body payload
    mock_queue_tcp_payload("POST / HTTP/1.1\r\nContent-Length: 100\r\n\r\nshort");
    // 3. Valid POST to exit the loop
    mock_queue_tcp_payload("POST / HTTP/1.1\r\nContent-Length: 9\r\n\r\nssid=Pass");

    clock_state_t state = {.wifi_initialized = false};
    wifi_error_t err = start_wifi_access_point(NULL, mock_store_config_success, &state.wifi_initialized);

    ASSERT_WITH_MESSAGE(err, WIFI_OK, "Should ignore incomplete packets and wait for valid one");
    ASSERT_WITH_MESSAGE(config_save_count, 1, "Should only store the valid payload");

    return 0;
}

static int test_ap_invalid_numeric_rejected(void)
{
    reset_wifi_test_state();

    mock_queue_tcp_payload("POST / HTTP/1.1\r\nContent-Length: 5\r\n\r\ncto=0");
    mock_queue_tcp_payload("POST / HTTP/1.1\r\nContent-Length: 9\r\n\r\nssid=Pass");

    clock_state_t state = {.wifi_initialized = false};
    wifi_error_t err = start_wifi_access_point(NULL, mock_store_config_success, &state.wifi_initialized);

    ASSERT_WITH_MESSAGE(err, WIFI_OK, "Should reject invalid timeout but continue");
    ASSERT_WITH_MESSAGE(config_save_count, 1, "Only valid payload should be stored");
    ASSERT_WITH_MESSAGE(strcmp(last_config.wifi_ssid, "Pass"), 0, "Valid payload should eventually persist");

    return 0;
}

static int test_ap_tcp_error_handling(void)
{
    reset_wifi_test_state();

    // Inject a TCP connection reset (ERR_RST) into the event loop at T+50ms
    mock_inject_tcp_error(ERR_RST, 50);
    // Send valid POST that fires after the error to finish the test gracefully
    mock_queue_tcp_payload("POST / HTTP/1.1\r\nContent-Length: 9\r\n\r\nssid=Pass");

    clock_state_t state = {.wifi_initialized = false};
    wifi_error_t err = start_wifi_access_point(NULL, mock_store_config_success, &state.wifi_initialized);

    ASSERT_WITH_MESSAGE(err, WIFI_OK, "tcp_server_err should clean up cleanly without crashing");
    return 0;
}

static int test_flash_config_modes(void)
{
    RESET_MOCK_CONFIG();
    mock_ctx.inject.factory_reset_pressed = 1;
    mock_ctx.inject.cyw43_arch_init_fail = 1;
    EXECUTE_TEST("Factory reset on boot", EXPECT_FAIL);
    CHECK_WATCHDOG_RESET_OK();
    ASSERT_WITH_MESSAGE(mock_ctx.spy.cyw43_arch_init_fail, 1, "Wi-Fi init started");
    ASSERT_WITH_MESSAGE(mock_ctx.spy.watchdog_reboot_called, 1, "Watchdog reboot called");
    return 0;
}

int main(const int argc, const char *argv[])
{
    int status = 0;
    if (argc > 1) {
        if (strcmp(argv[1], "--verbose") == 0) {
            test_verbose = 1;
        } else {
            fprintf(stderr, "Warning: unknown command-line argument %s\n", argv[1]);
        }
    }

    status |= run_test(test_lcd, "Basic LCD hardware");
    status |= run_test(test_dst, "Daylight savings");
    status |= run_test(test_clock_timer_paths, "Clock timer paths");
    status |= run_test(test_clock_start_timer_failures, "Clock startup timer failures");
    status |= run_test(test_ntp_time, "NTP time checks");
    status |= run_test(test_wifi_errors, "Wi-Fi init error");
    status |= run_test(test_connect_to_wifi_direct, "Wi-Fi entry point: connect_to_wifi");
    status |= run_test(test_start_wifi_access_point_direct, "Wi-Fi entry point: start_wifi_access_point");
    status |= run_test(test_wifi_tcp_callback_paths, "Wi-Fi TCP callback paths");
    status |= run_test(test_wifi_startup_failures, "Wi-Fi startup failures");
    status |= run_test(test_wifi_request_parser_paths, "Wi-Fi request parser paths");
    status |= run_test(test_dns_lookups, "DNS lookups");
    status |= run_test(test_ntp_unsynchronized_server, "NTP unsynchronized server");
    status |= run_test(test_ntp_errors, "NTP errors");
    status |= run_test(test_error_strings, "Status error strings");
    status |= run_test(test_watchdog, "Watchdog");
    status |= run_test(test_wifi_config_urls, "Wi-Fi AP: URL tests");
    status |= run_test(test_ap_reuse_config, "Wi-Fi AP: reuse old config");
    status |= run_test(test_wifi_ap_limits, "Wi-Fi AP limits");
    status |= run_test(test_ap_init_fails_cyw43, "Wi-Fi AP: CYW43 init fails");
    status |= run_test(test_ap_wifi_already_initialized, "Wi-Fi AP: Short-circuit already initialized");
    status |= run_test(test_ap_success_full_post, "Wi-Fi AP: Successful POST payload processing");
    status |= run_test(test_ap_url_decoding, "Wi-Fi AP: URL encoded payload logic");
    status |= run_test(test_ap_url_decode_malformed, "Wi-Fi AP: Malformed URL hex decoding");
    status |= run_test(test_ap_dst_rule_fallback, "Wi-Fi AP: DST Rule fallback mapping");
    status |= run_test(test_ap_get_config_page, "Wi-Fi AP: Handle GET config requests");
    status |= run_test(test_ap_get_redirect, "Wi-Fi AP: Handle captive portal redirects");
    status |= run_test(test_ap_post_save_fails, "Wi-Fi AP: Flash write failure recovery");
    status |= run_test(test_ap_incomplete_requests, "Wi-Fi AP: Ignore incomplete TCP streams");
    status |= run_test(test_ap_invalid_numeric_rejected, "Wi-Fi AP: Reject invalid numeric fields");
    status |= run_test(test_ap_tcp_error_handling, "Wi-Fi AP: Handle TCP reset/abort events");
    status |= run_test(test_flash_config_modes, "Flash config modes");

    return status;
}
