masaccio/picow_day_clock/src/test_main.c

#include <setjmp.h>

#include "clock.h"
#include "mock.h"
#include "ntp.h"
#include "test.h"
#include "watchdog.h"
#include "wifi.h"

extern int test_main(void);

jmp_buf fatal_reset_jmp_buf;
persistent_state_t persistent_state;

void fatal_reset(clock_state_t *state, ntp_error_t ntp_error, wifi_error_t wifi_error)
{
    (void)state;
    persistent_state.ntp_error = ntp_error;
    persistent_state.wifi_error = wifi_error;
    mock_ctx.spy.fatal_ntp_error = ntp_error;
    mock_ctx.spy.fatal_wifi_error = wifi_error;

    watchdog_reboot((uint32_t)0, SRAM_END, (uint32_t)0 /* delay_ms */);

    if (mock_ctx.inject.fatal_reset_no_longjmp)
        return;

    // Returns into main() which will then exit with status=1
    longjmp(fatal_reset_jmp_buf, 1);
}

int test_main(void)
{
    clock_state_t state;

    test_printf("Test init\n");

    if (setjmp(fatal_reset_jmp_buf)) {
        if (mock_ctx.spy.fatal_reset_caught)
            // Don't get caught in a loop of watchdog reboots
            return 1;

        mock_ctx.spy.fatal_reset_caught = 1;
        // Reboot the clock to ensure that fault state is captured.
        // Don't enter the main loop and instead return to test harness.
        clock_init(&state);
        return 1;
    }

    mock_ctx.spy.watchdog_reboot_called = 0;

    clock_init(&state);
    clock_start(&state);

    while (1) {
        if (state.ntp_state.status == NTP_FAILED) {
            fatal_reset(&state, state.ntp_state.error, WIFI_OK);
        } else if (mock_ctx.inject.exit_on_ntp_success && state.ntp_state.status == NTP_SUCCESS) {
            // Some tests expect normal operation, but we still need to return to the test harness
            break;
        } else if (mock_ctx.inject.exit_after_ms && mock_ctx.spy.boot_time_ms >= mock_ctx.inject.exit_after_ms) {
            break;
        }
        clock_task(&state);
        sleep_ms(10);
    }

    return 0;
}
